manolitto/openvlex2/gluing-stencil/img/gluing_with_base_clamps.jpg

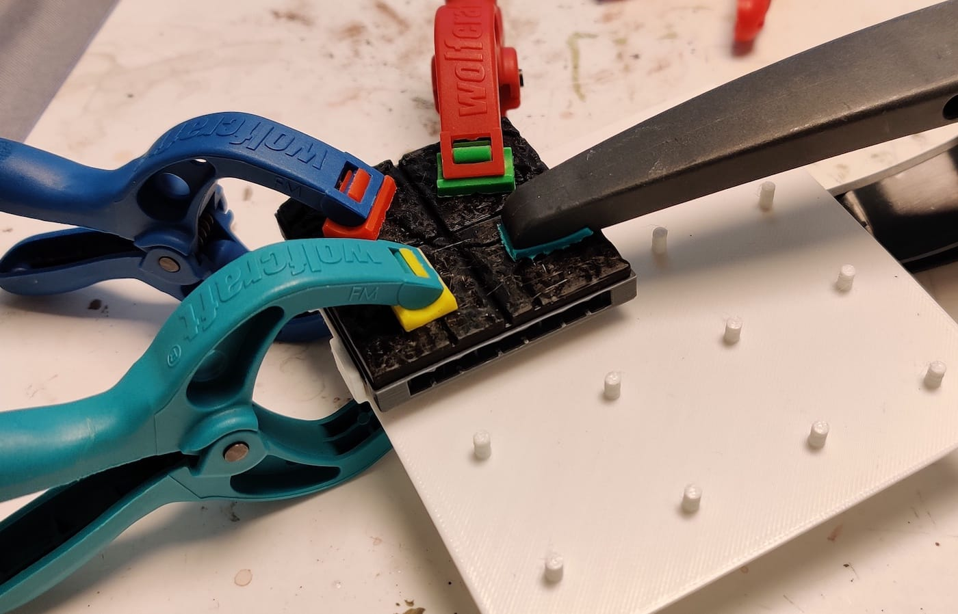
gluing-stencil/img/gluing_with_base_clamps.jpg
