manolitto/openvlex2/gluing-stencil/img/gluing_with_base_clamps_upside_down.jpg

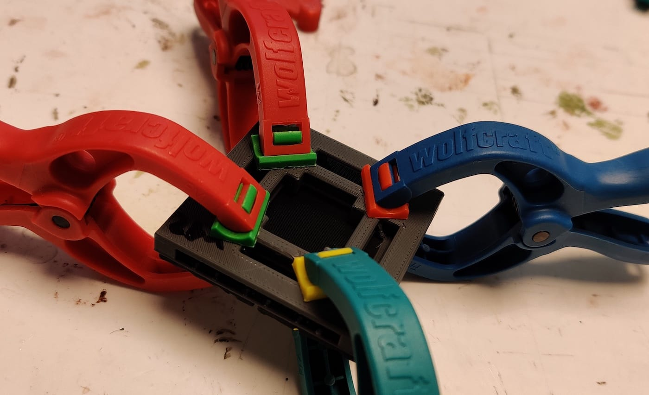
gluing-stencil/img/gluing_with_base_clamps_upside_down.jpg
