manolitto/openvlex2/gluing-stencil/img/gluing_with_base_remove.jpg

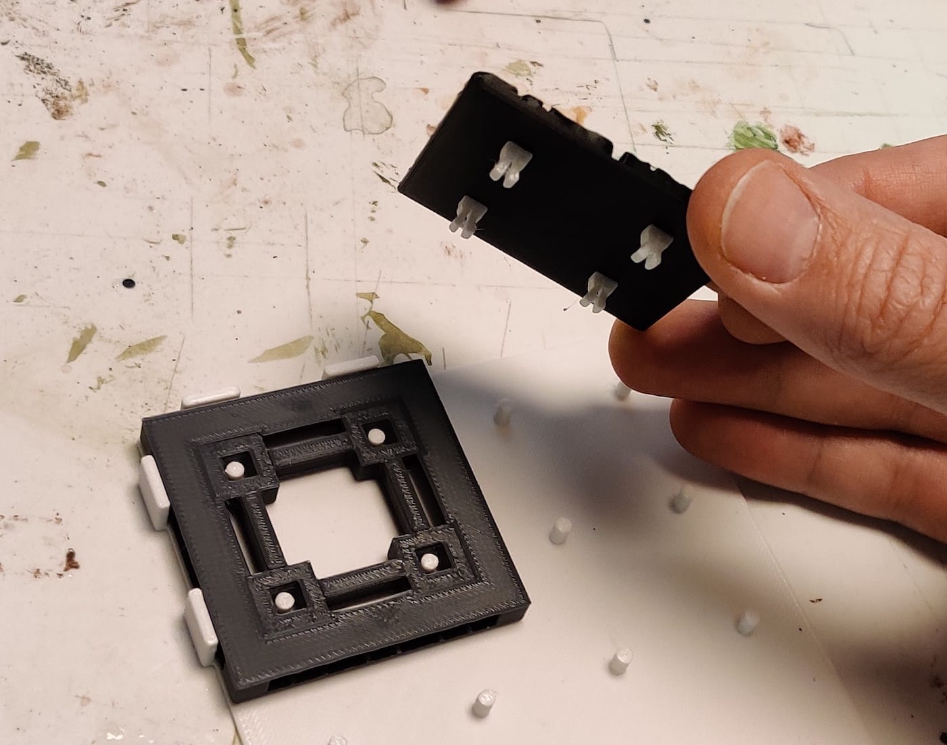
gluing-stencil/img/gluing_with_base_remove.jpg
