manolitto/openvlex2/img/img002.jpg

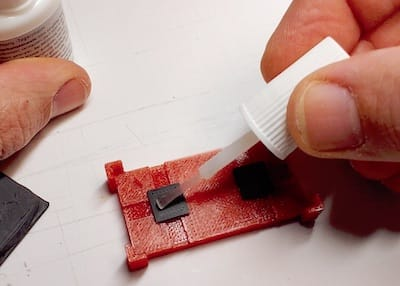
img/img002.jpg
