manolitto/openvlex2/img/img003.jpg

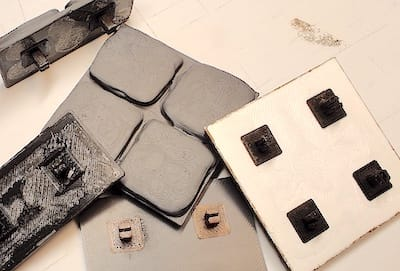
img/img003.jpg
