manolitto/openvlex2/img/img013.jpg

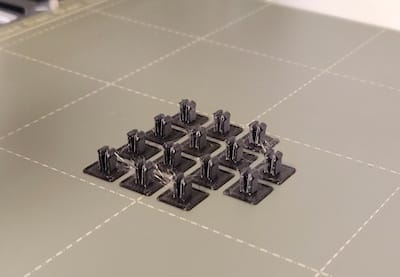
img/img013.jpg
