manolitto/openvlex2/img/stairs/IMG_20210401_234859.jpg

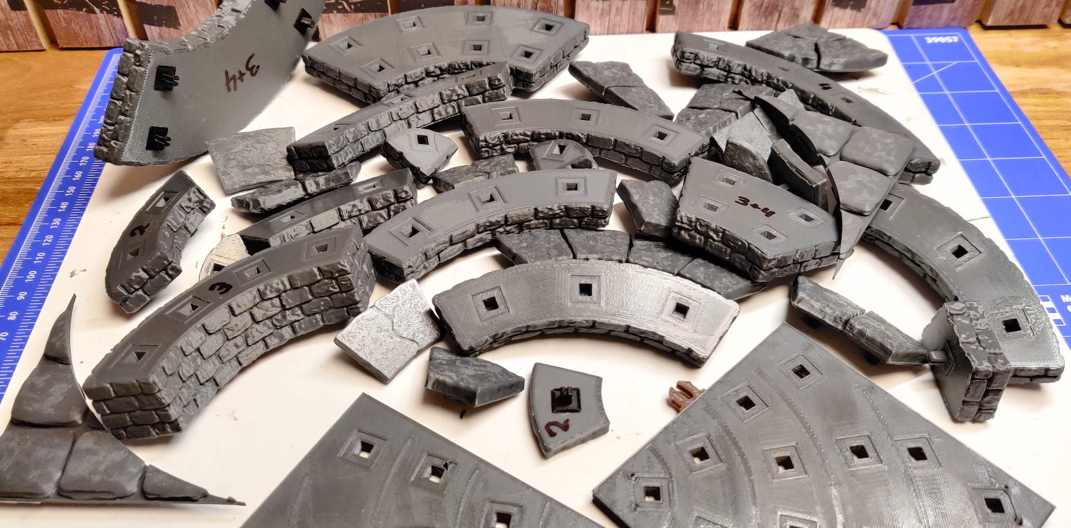
img/stairs/IMG_20210401_234859.jpg
