manolitto/openvlex2/img/stairs/IMG_20210401_235115.jpg

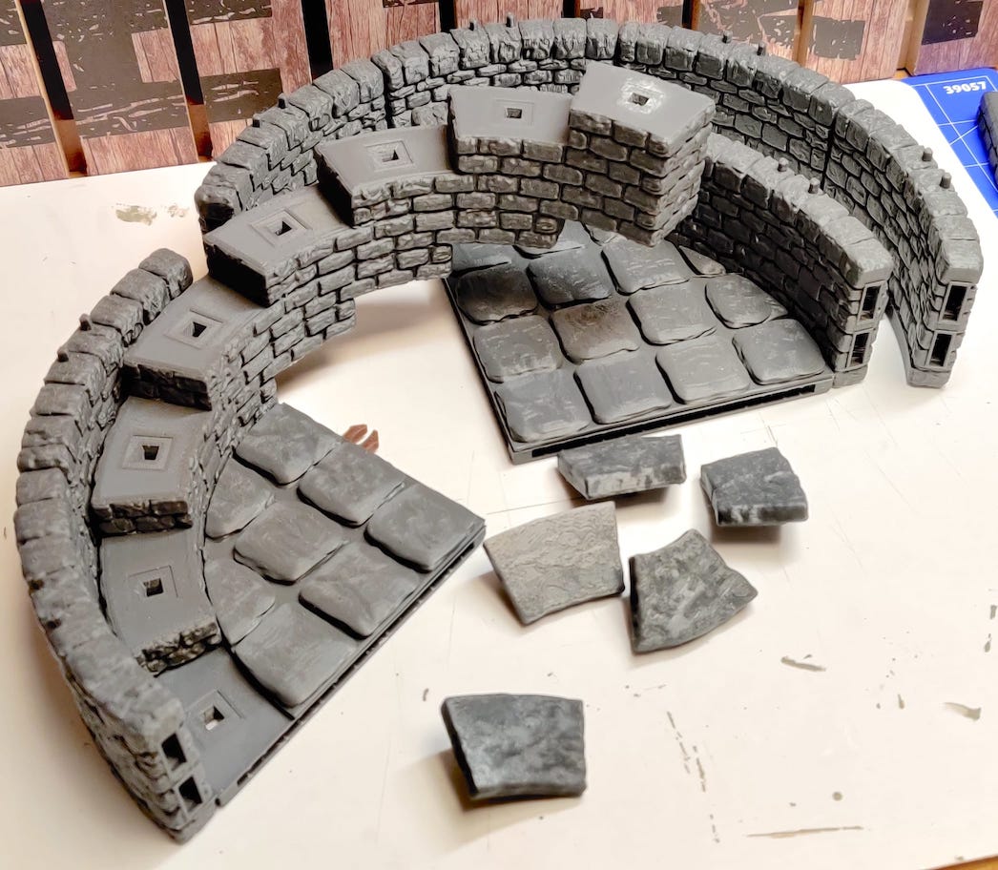
img/stairs/IMG_20210401_235115.jpg
