manolitto/openvlex2/socket_negatives/openvlex.bottom_socket_negative.square.1x1.large.stl

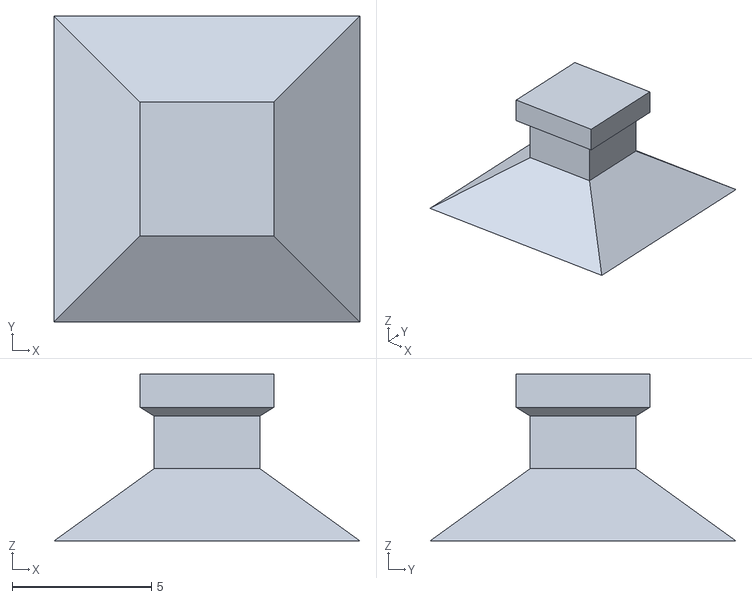
[picture p82: CAD file, 2022-04-11]
socket_negatives/openvlex.bottom_socket_negative.square.1x1.large.stl
11.0 x 11.0 x 6.00
