manolitto/openvlex2/stairs_and_risers/dungeon_stone/curved/dungeon_stone_stairs.curved.inch.riser.1+2x45°x0.25.openvlex.radial.stl

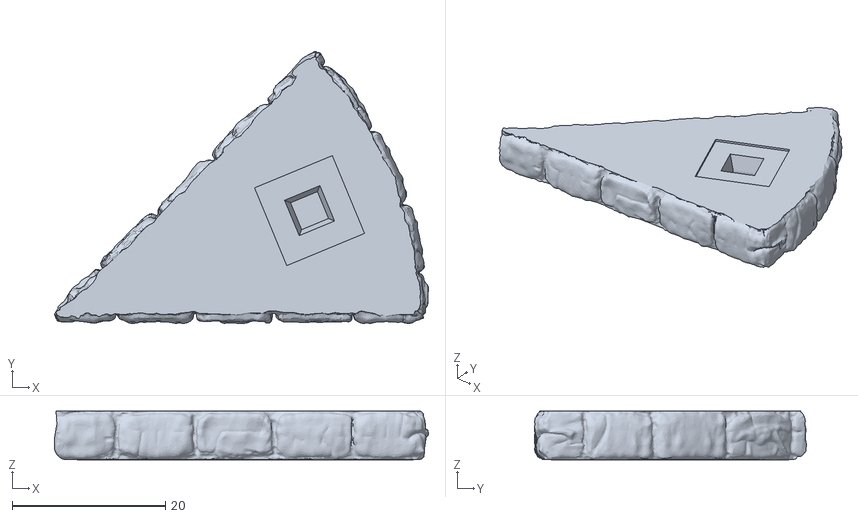
[picture p84: CAD file, 2021-07-12]
stairs_and_risers/dungeon_stone/curved/dungeon_stone_stairs.curved.inch.riser.1+2x45°x0.25.openvlex.radial.stl
48.9 x 35.5 x 6.35
