manolitto/openvlex2/stairs_and_risers/dungeon_stone/square/dungeon_stone_stairs.square.inch.riser_base.1x1x0.5.NS.openvlex.top_and_bottom.stl

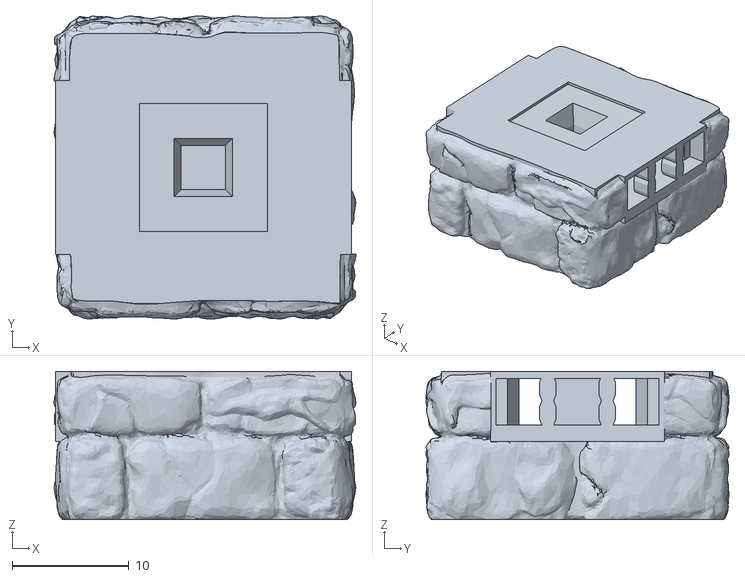
[picture p85: CAD file, 2021-07-12]
stairs_and_risers/dungeon_stone/square/dungeon_stone_stairs.square.inch.riser_base.1x1x0.5.NS.openvlex.top_and_bottom.stl
25.9 x 26.0 x 12.7
