manolitto/openvlex2/stairs_and_risers/plain/backwards_compatible/plain#riser+square,interlayer_half.2x2.openvlex,backwards_compatible.stl

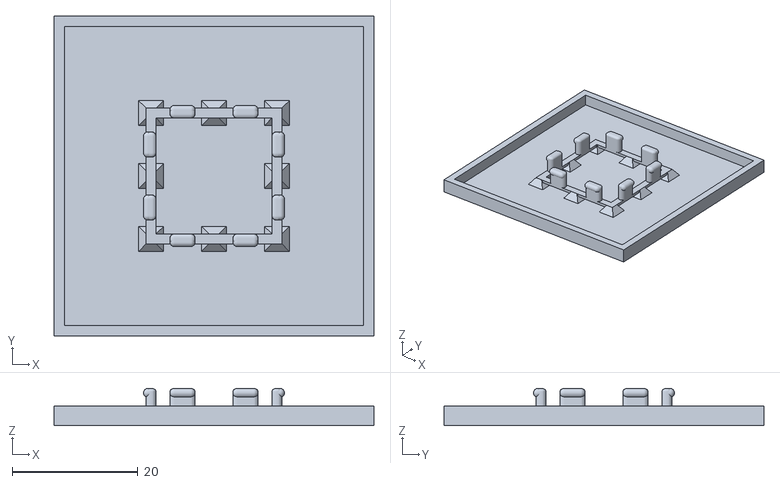
[picture p86: CAD file, 2022-01-03]
stairs_and_risers/plain/backwards_compatible/plain#riser+square,interlayer_half.2x2.openvlex,backwards_compatible.stl
50.8 x 50.8 x 5.90
