manolitto/openvlex2/stairs_and_risers/roof/roof+attic_support_block.4x.stl

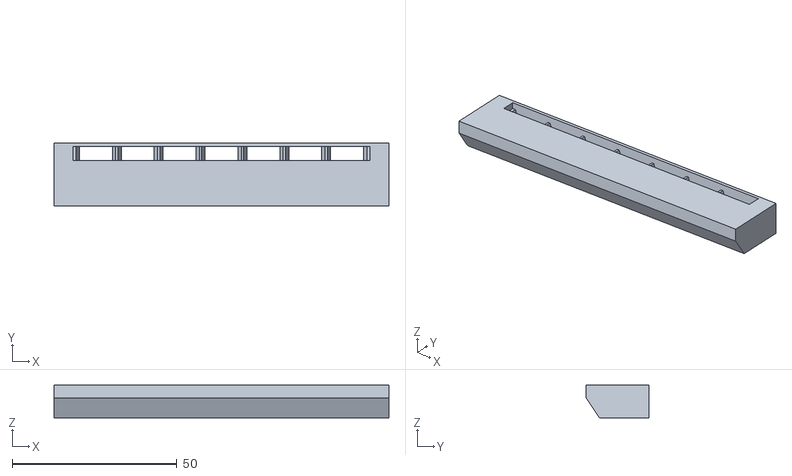
[picture p88: CAD file, 2022-01-11]
stairs_and_risers/roof/roof+attic_support_block.4x.stl
101.6 x 19.0 x 10.0
