manolitto/openvlex2/stairs_and_risers/towne/square/towne_stairs.square.inch.riser.1x1x1.0.openvlex.stl

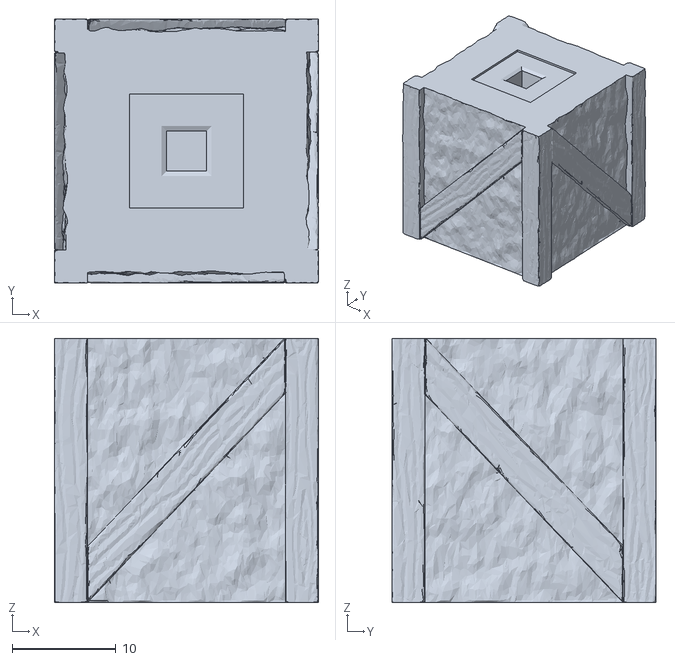
[picture p89: CAD file, 2021-04-06]
stairs_and_risers/towne/square/towne_stairs.square.inch.riser.1x1x1.0.openvlex.stl
25.4 x 25.4 x 25.4
