manolitto/openvlex2/storage/openvlex.storage_base_clip.floor.2_inch.stl

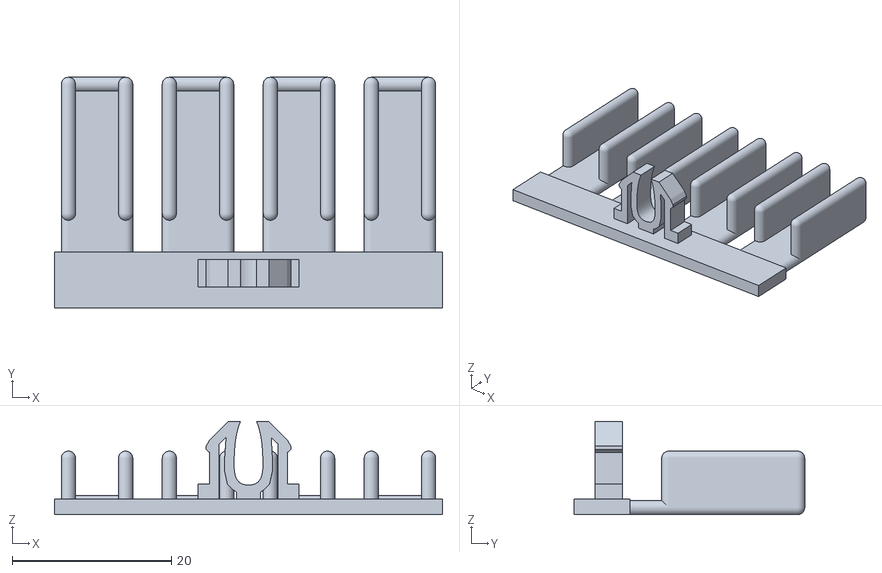
[picture p90: CAD file, 2021-04-06]
storage/openvlex.storage_base_clip.floor.2_inch.stl
48.8 x 29.0 x 11.7
