manolitto/openvlex2/bases/plain/magnetic,openlock,openvlex+dual_parts/plain#base+square.7x3.magnetic,openlock,openvlex+lower_part.stl

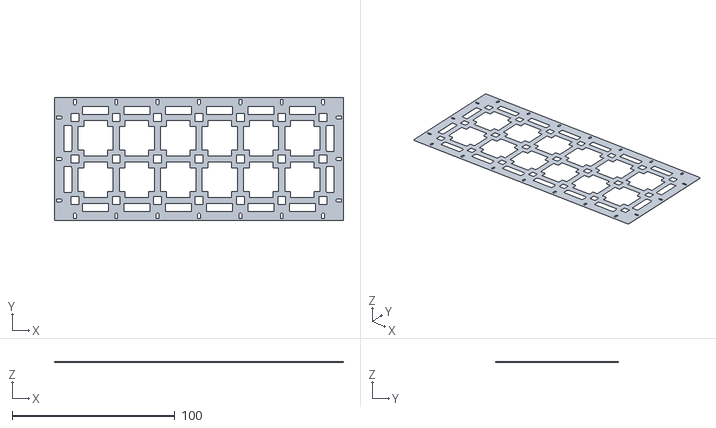
[picture p92: CAD file, 2022-01-04]
bases/plain/magnetic,openlock,openvlex+dual_parts/plain#base+square.7x3.magnetic,openlock,openvlex+lower_part.stl
177.4 x 75.8 x 0.6
