manolitto/openvlex2/bases/plain/magnetic,openlock,openvlex+radial/plain#base+square.4x4.magnetic.openlock,openvlex+radial,upper_part.stl

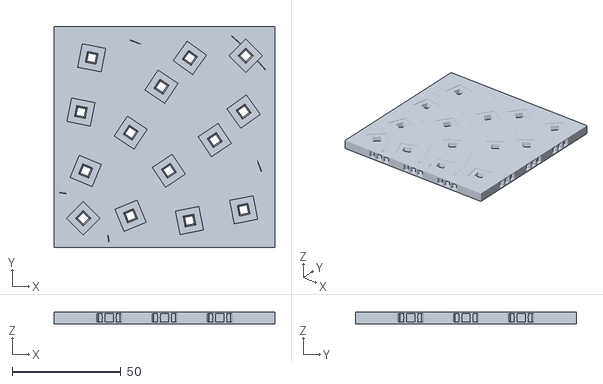
[picture p93: CAD file, 2021-11-02]
bases/plain/magnetic,openlock,openvlex+radial/plain#base+square.4x4.magnetic.openlock,openvlex+radial,upper_part.stl
101.6 x 101.6 x 5.40
