manolitto/openvlex2/bases/plain/openlock,openflex+radial/plain#base+square.2x2.openlock,openvlex+radial.stl

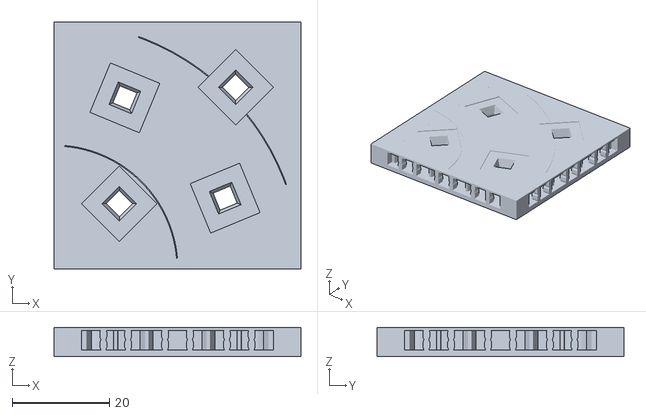
[picture p94: CAD file, 2021-11-02]
bases/plain/openlock,openflex+radial/plain#base+square.2x2.openlock,openvlex+radial.stl
50.8 x 50.8 x 6.01
