manolitto/openvlex2/bases/plain/POC/base.plain.square.inch.2x2.magnetic.openlock.openvlex_upper.stl

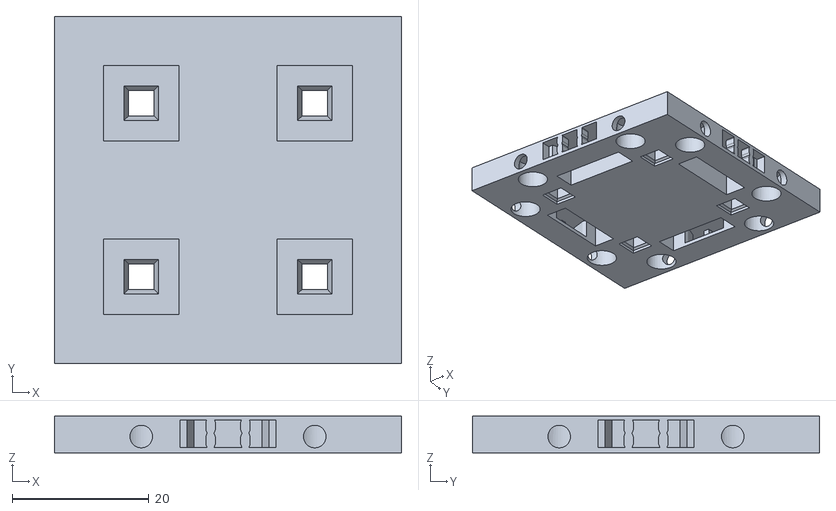
[picture p96: CAD file, 2021-11-02]
bases/plain/POC/base.plain.square.inch.2x2.magnetic.openlock.openvlex_upper.stl
50.8 x 50.8 x 5.40
