manolitto/openvlex2/bases/separate_wall/rough_stone#base.A.openlock,openvlex.stl

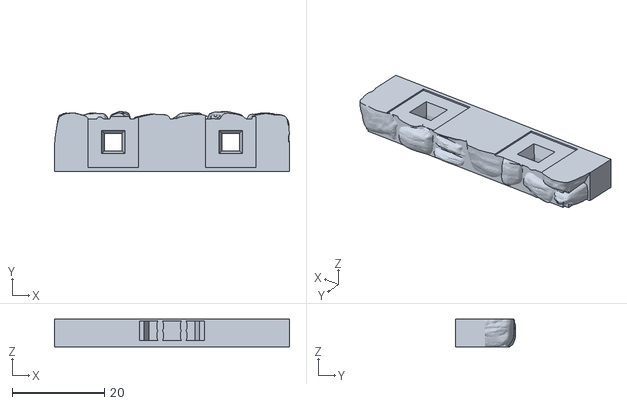
[picture p97: CAD file, 2022-01-12]
bases/separate_wall/rough_stone#base.A.openlock,openvlex.stl
50.8 x 13.0 x 6.00
