manolitto/openvlex2/bases/sewer/sewer#base+square.1x1.openlock,openvlex+corner.stl

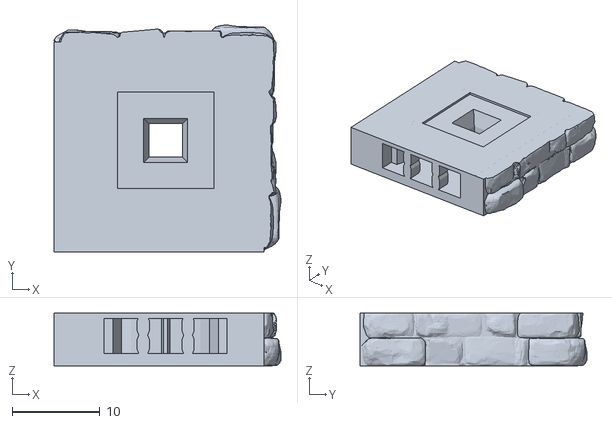
[picture p98: CAD file, 2021-11-30]
bases/sewer/sewer#base+square.1x1.openlock,openvlex+corner.stl
25.8 x 25.8 x 6.01
