manolitto/openvlex2/gluing-stencil/openvlex_gluing_stencil.4x3.stl

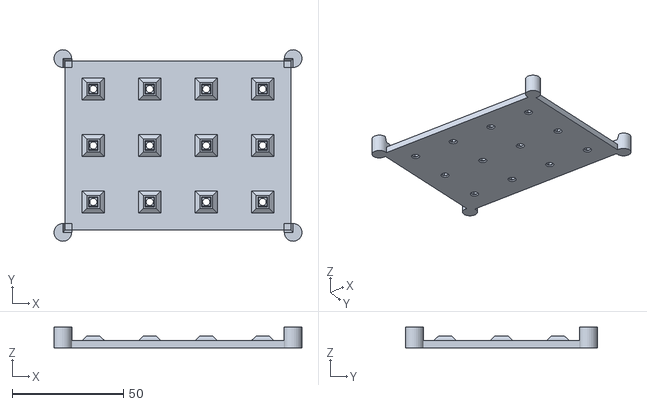
[picture p99: CAD file, 2022-04-11]
gluing-stencil/openvlex_gluing_stencil.4x3.stl
111.6 x 86.2 x 9.40
