manolitto/openvlex2/jacks/openvlex.double_jack (v2.5.0).stl

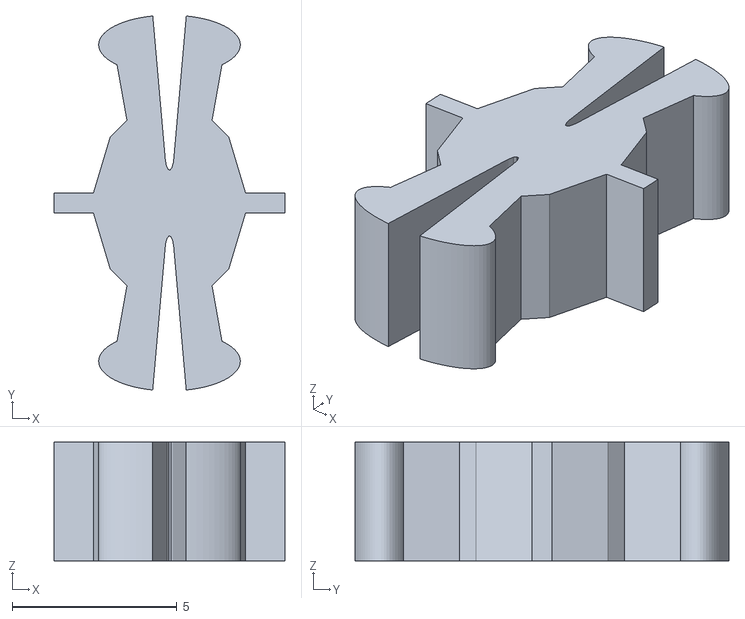
[picture p100: CAD file, 2022-04-11]
jacks/openvlex.double_jack (v2.5.0).stl
7.00 x 11.3 x 3.60
