manolitto/openvlex2/openflex1_to_openvlex2_adapter/openflex1_to_openvlex2_adapter_plate.small.1x1.stl

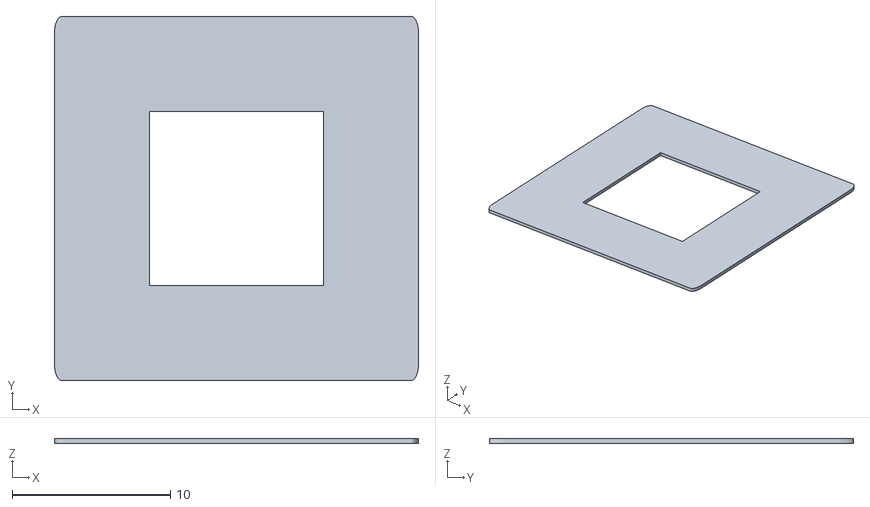
[picture p101: CAD file, 2021-03-14]
openflex1_to_openvlex2_adapter/openflex1_to_openvlex2_adapter_plate.small.1x1.stl
23.0 x 23.0 x 0.296
