manolitto/openvlex2/socket_negatives/openvlex.bottom_socket_negative.square.4x2.square.stl

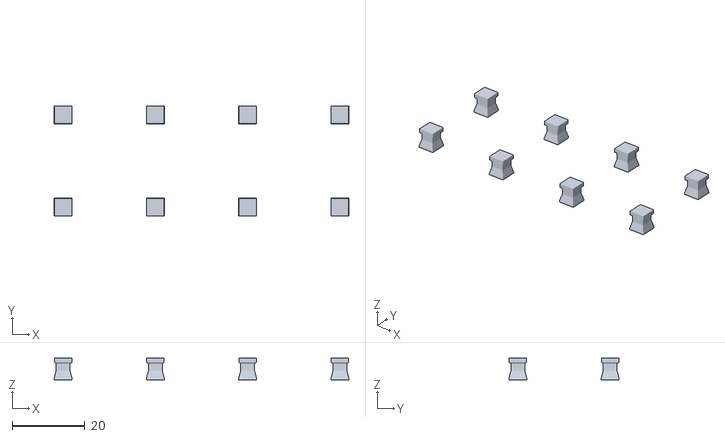
[picture p102: CAD file, 2021-04-16]
socket_negatives/openvlex.bottom_socket_negative.square.4x2.square.stl
81.2 x 30.4 x 6.00
