manolitto/openvlex2/stairs_and_risers/dungeon_stone/curved/dungeon_stone_stairs.curved.inch.riser.4x45°x0.5.openvlex.radial.stl

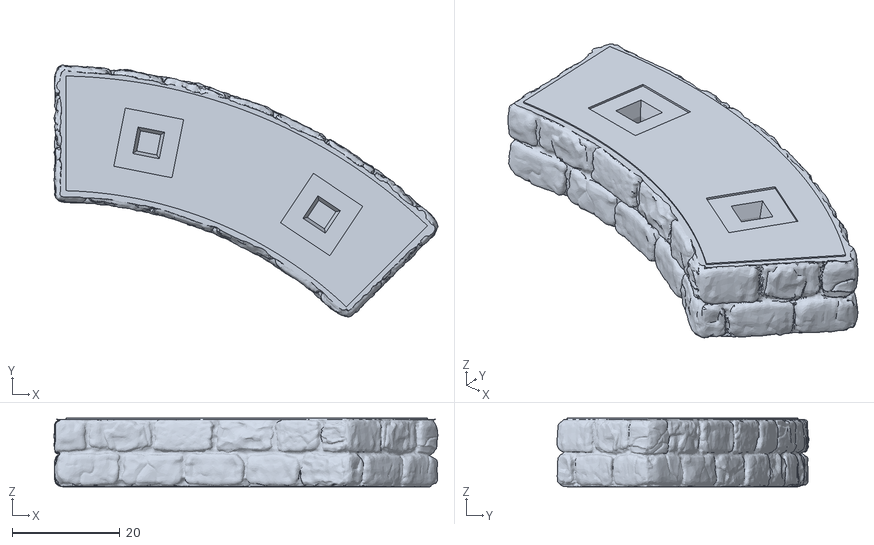
[picture p104: CAD file, 2021-03-31]
stairs_and_risers/dungeon_stone/curved/dungeon_stone_stairs.curved.inch.riser.4x45°x0.5.openvlex.radial.stl
71.1 x 46.7 x 12.7
