manolitto/openvlex2/stairs_and_risers/plain/backwards_compatible/plain#riser+square,platform.2x2.openvlex,backwards_compatible.stl

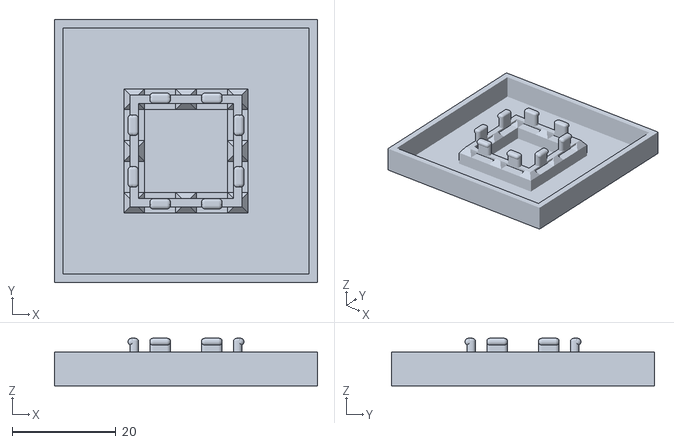
[picture p106: CAD file, 2022-01-03]
stairs_and_risers/plain/backwards_compatible/plain#riser+square,platform.2x2.openvlex,backwards_compatible.stl
50.8 x 50.8 x 9.20
