manolitto/openvlex2/stairs_and_risers/plain/plain#riser+square,platform.1x1.openvlex.stl

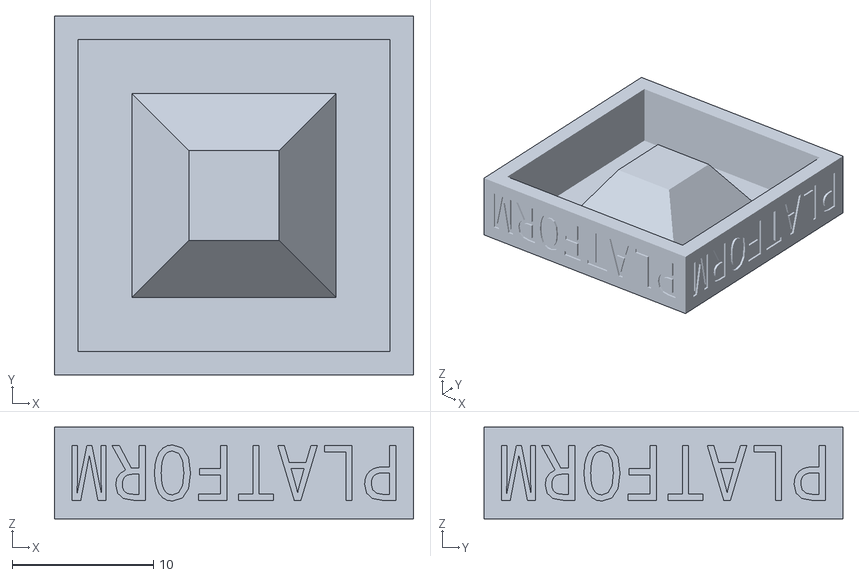
[picture p107: CAD file, 2022-04-11]
stairs_and_risers/plain/plain#riser+square,platform.1x1.openvlex.stl
25.4 x 25.4 x 6.50
