manolitto/openvlex2/stairs_and_risers/towne/square/towne_stairs.square.inch.riser.2x2x1.0.openvlex.stl

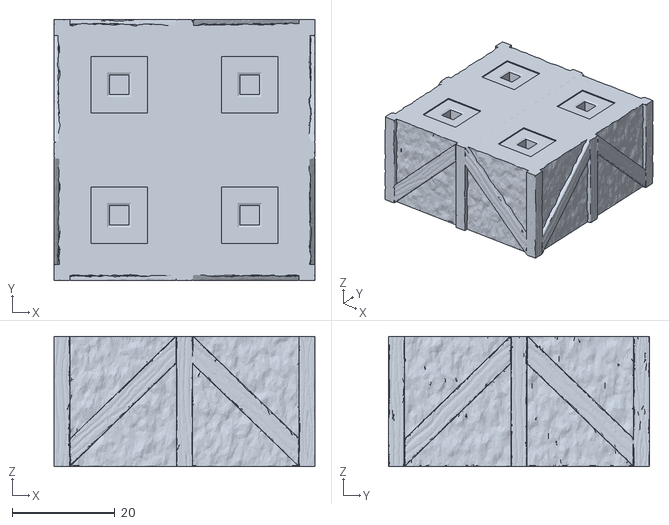
[picture p108: CAD file, 2021-04-06]
stairs_and_risers/towne/square/towne_stairs.square.inch.riser.2x2x1.0.openvlex.stl
50.8 x 50.8 x 25.4
