manolitto/openvlex2/bases/dungeon_stone/dungeon_stone#base+square.2x1.openlock,openvlex+corner-left.stl

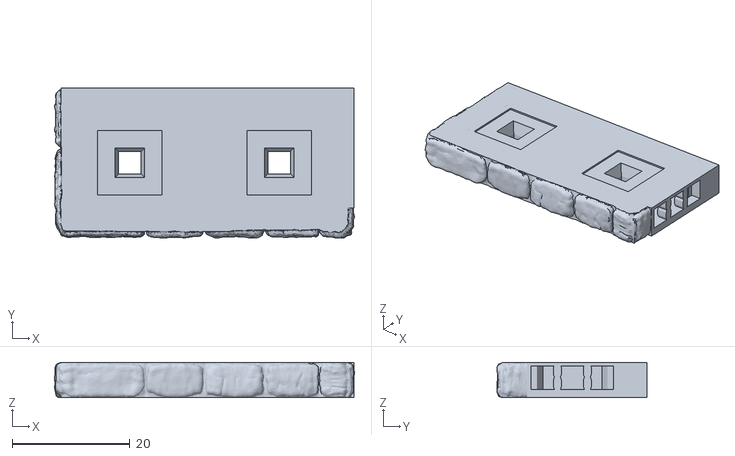
[picture p109: CAD file, 2021-04-17]
bases/dungeon_stone/dungeon_stone#base+square.2x1.openlock,openvlex+corner-left.stl
51.0 x 25.5 x 6.01
