manolitto/openvlex2/bases/plain/magnetic,openlock,openvlex+dual_parts/plain#base+square.8x5.magnetic,openlock,openvlex+border_only,lower_part.stl

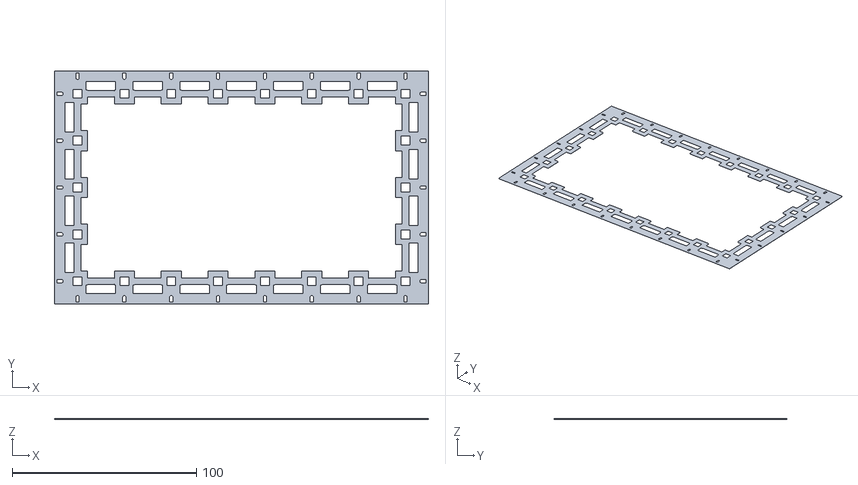
[picture p110: CAD file, 2022-01-04]
bases/plain/magnetic,openlock,openvlex+dual_parts/plain#base+square.8x5.magnetic,openlock,openvlex+border_only,lower_part.stl
202.8 x 126.6 x 0.6
