manolitto/openvlex2/bases/plain/magnetic,openlock,openvlex+radial/plain#base+square.2x2.magnetic.openlock,openvlex+radial,upper_part.stl

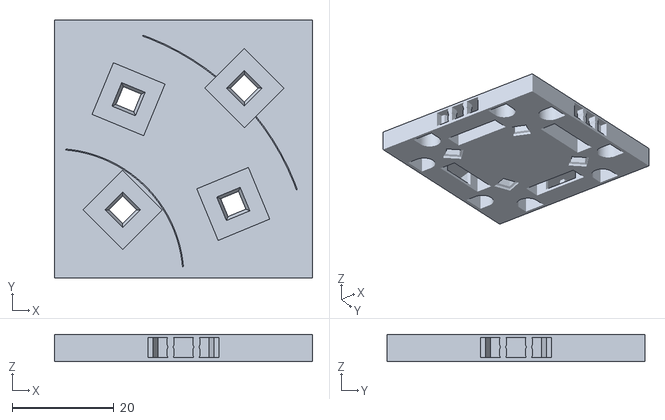
[picture p111: CAD file, 2021-11-02]
bases/plain/magnetic,openlock,openvlex+radial/plain#base+square.2x2.magnetic.openlock,openvlex+radial,upper_part.stl
50.8 x 50.8 x 5.40
