manolitto/openvlex2/bases/plain/openlock,openflex+radial/plain#base+square.3x3.openlock,openvlex+radial.stl

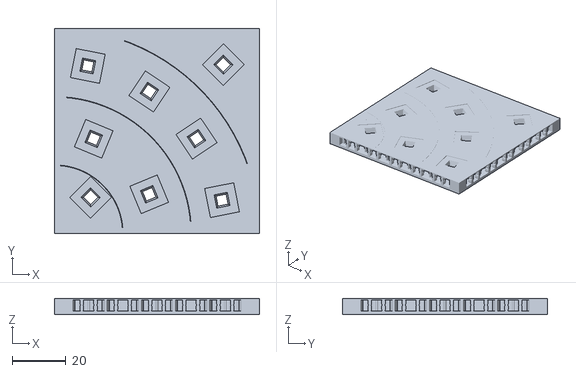
[picture p113: CAD file, 2021-11-02]
bases/plain/openlock,openflex+radial/plain#base+square.3x3.openlock,openvlex+radial.stl
76.2 x 76.2 x 6.01
