manolitto/openvlex2/bases/plain/openlock,openvlex/plain#base+square.8x3.openlock,openvlex+border_only.stl

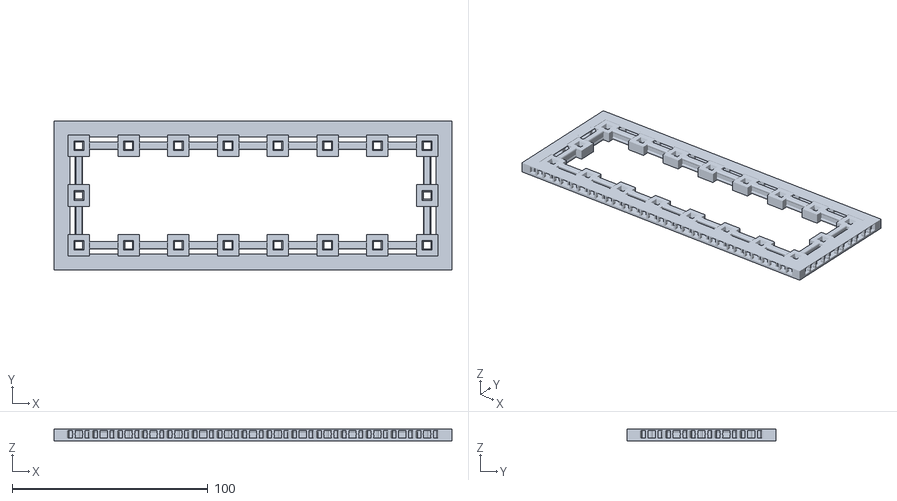
[picture p114: CAD file, 2022-01-04]
bases/plain/openlock,openvlex/plain#base+square.8x3.openlock,openvlex+border_only.stl
203.2 x 76.2 x 6.01
