manolitto/openvlex2/bases/sewer/sewer#base+square.2x1.openlock,openvlex+edge.stl

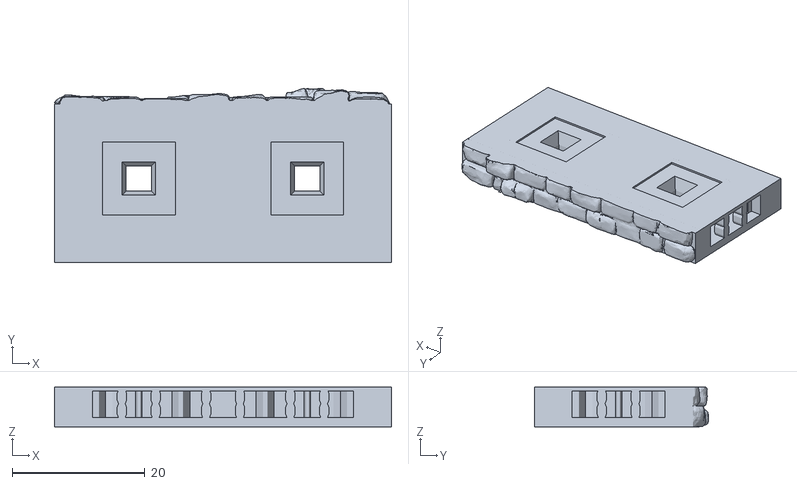
[picture p115: CAD file, 2021-11-30]
bases/sewer/sewer#base+square.2x1.openlock,openvlex+edge.stl
50.8 x 26.3 x 6.01
