manolitto/openvlex2/gluing-stencil/openvlex_gluing_stencil.4x2.stl

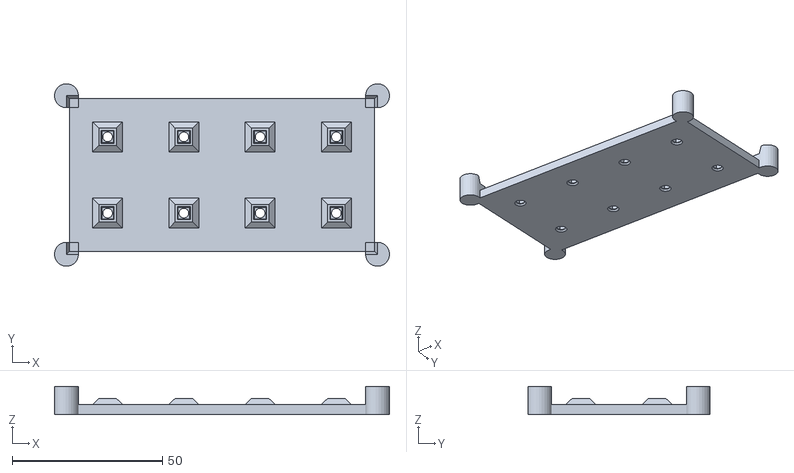
[picture p116: CAD file, 2022-04-11]
gluing-stencil/openvlex_gluing_stencil.4x2.stl
111.6 x 60.8 x 9.40
