manolitto/openvlex2/openflex1_to_openvlex2_adapter/openflex1_to_openvlex2_adapter_plate.small.2x1.stl

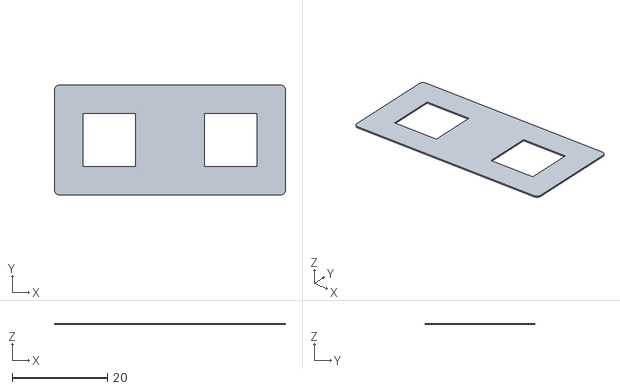
[picture p117: CAD file, 2021-03-14]
openflex1_to_openvlex2_adapter/openflex1_to_openvlex2_adapter_plate.small.2x1.stl
48.4 x 23.0 x 0.296
