manolitto/openvlex2/socket_negatives/openvlex.top_socket_negative.square.4x2.square.stl

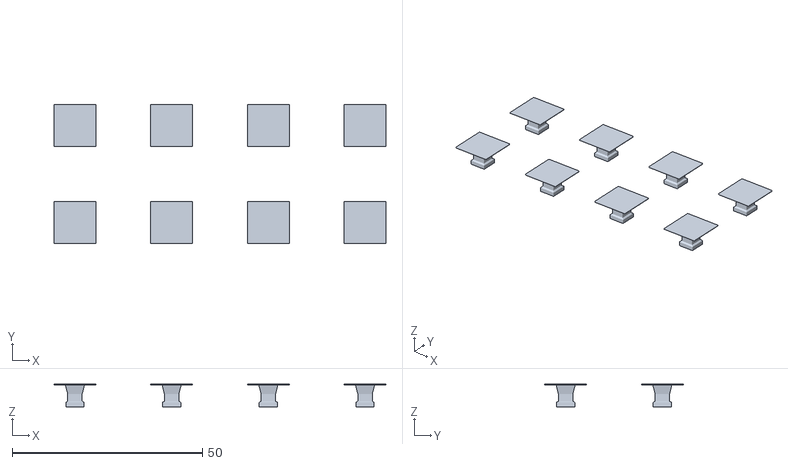
[picture p118: CAD file, 2021-04-16]
socket_negatives/openvlex.top_socket_negative.square.4x2.square.stl
87.2 x 36.4 x 6.00
