manolitto/openvlex2/stairs_and_risers/cut_stone/square/cut_stone_stairs.square.inch.riser.2x2x0.5.openvlex.stl

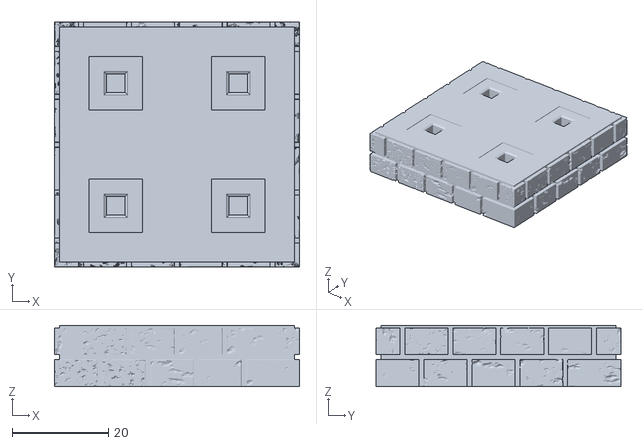
[picture p119: CAD file, 2021-04-06]
stairs_and_risers/cut_stone/square/cut_stone_stairs.square.inch.riser.2x2x0.5.openvlex.stl
50.8 x 50.8 x 12.7
