manolitto/openvlex2/stairs_and_risers/dungeon_stone/curved/dungeon_stone_stairs.curved.inch.riser.1+2x45°x0.5.openvlex.radial.stl

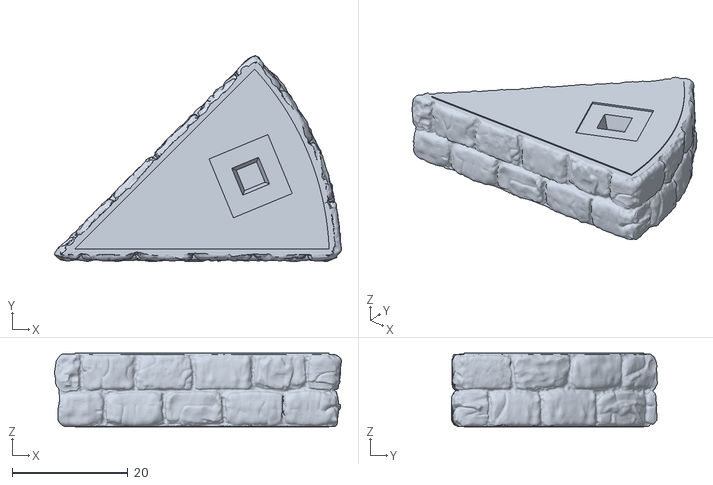
[picture p120: CAD file, 2021-03-27]
stairs_and_risers/dungeon_stone/curved/dungeon_stone_stairs.curved.inch.riser.1+2x45°x0.5.openvlex.radial.stl
49.6 x 35.6 x 12.7
