manolitto/openvlex2/stairs_and_risers/plain/plain#riser+square,low.2x2.openvlex,L-shape.stl

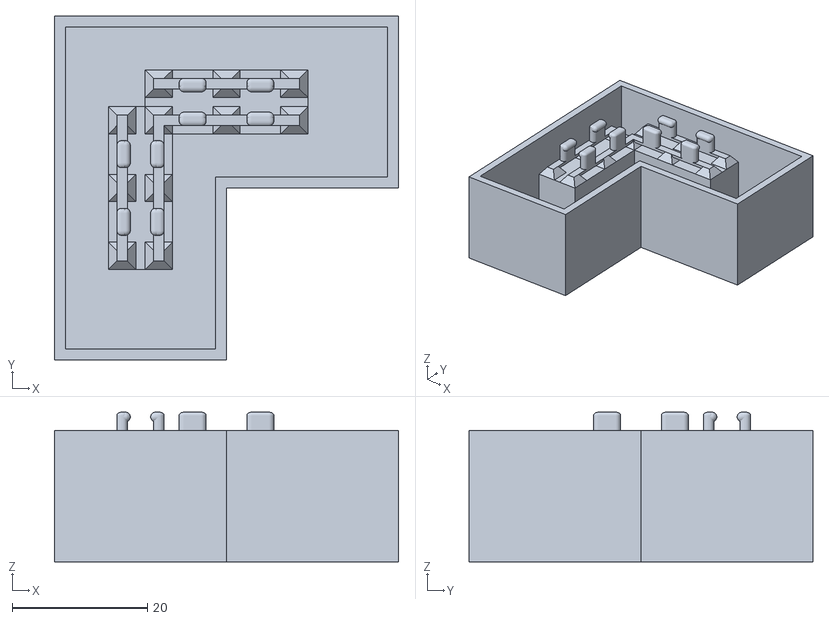
[picture p122: CAD file, 2022-04-11]
stairs_and_risers/plain/plain#riser+square,low.2x2.openvlex,L-shape.stl
50.8 x 50.8 x 22.1
