manolitto/openvlex2/stairs_and_risers/towne/square/towne_stairs.square.inch.riser.2x1x1.0.openvlex.stl

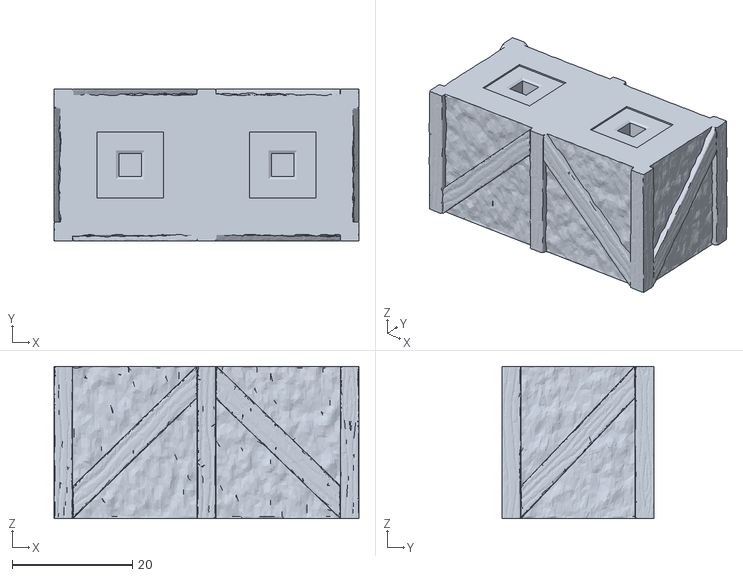
[picture p123: CAD file, 2021-04-06]
stairs_and_risers/towne/square/towne_stairs.square.inch.riser.2x1x1.0.openvlex.stl
50.8 x 25.4 x 25.4
