manolitto/openvlex2/bases/dungeon_stone/dungeon_stone#base+square.1x1.openlock,openvlex+corner.stl

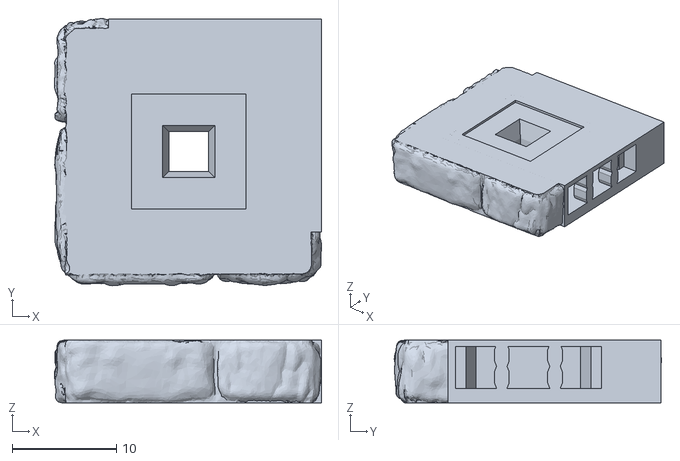
[picture p124: CAD file, 2021-04-17]
bases/dungeon_stone/dungeon_stone#base+square.1x1.openlock,openvlex+corner.stl
25.6 x 25.6 x 6.01
