manolitto/openvlex2/bases/plain/magnetic,openlock,openvlex+dual_parts/plain#base+square.4x4.magnetic,openlock,openvlex+border_only,lower_part.stl

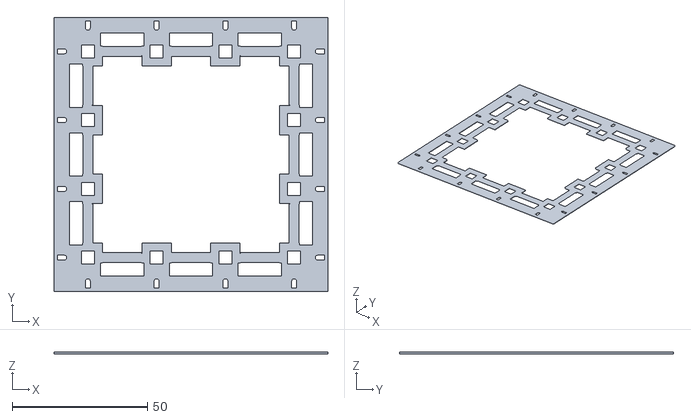
[picture p125: CAD file, 2022-01-04]
bases/plain/magnetic,openlock,openvlex+dual_parts/plain#base+square.4x4.magnetic,openlock,openvlex+border_only,lower_part.stl
101.2 x 101.2 x 0.6
