manolitto/openvlex2/bases/plain/magnetic,openlock,openvlex+radial/plain#base+square.3x3.magnetic.openlock,openvlex+radial,upper_part.stl

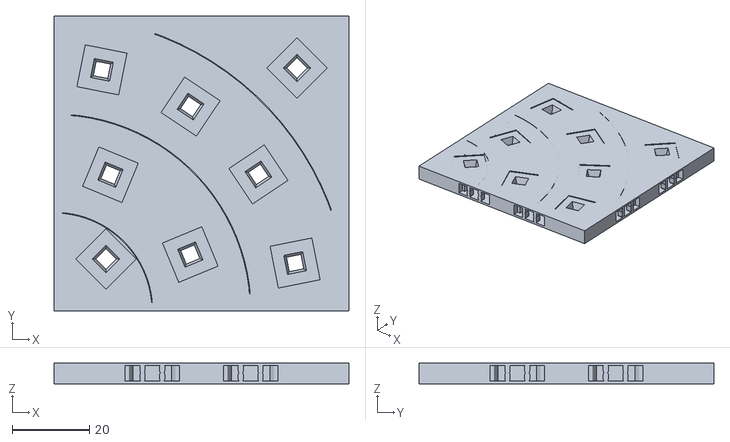
[picture p126: CAD file, 2021-11-02]
bases/plain/magnetic,openlock,openvlex+radial/plain#base+square.3x3.magnetic.openlock,openvlex+radial,upper_part.stl
76.2 x 76.2 x 5.40
