manolitto/openvlex2/bases/plain/openlock,openvlex/plain#base+square.7x7.openlock,openvlex+border_only.stl

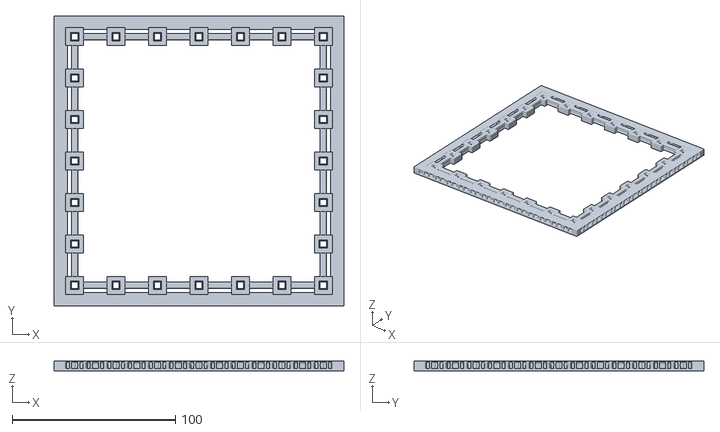
[picture p127: CAD file, 2022-01-04]
bases/plain/openlock,openvlex/plain#base+square.7x7.openlock,openvlex+border_only.stl
177.8 x 177.8 x 6.01
