manolitto/openvlex2/gluing-stencil/openvlex_gluing_stencil.4x1.stl

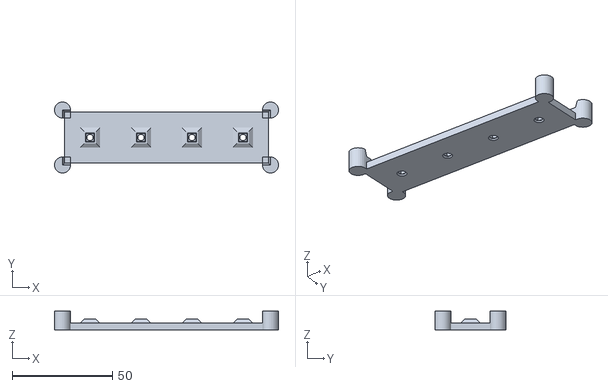
[picture p128: CAD file, 2022-04-11]
gluing-stencil/openvlex_gluing_stencil.4x1.stl
111.6 x 35.4 x 9.40
