manolitto/openvlex2/openflex1_to_openvlex2_adapter/openflex1_to_openvlex2_adapter_socket_with_support.stl

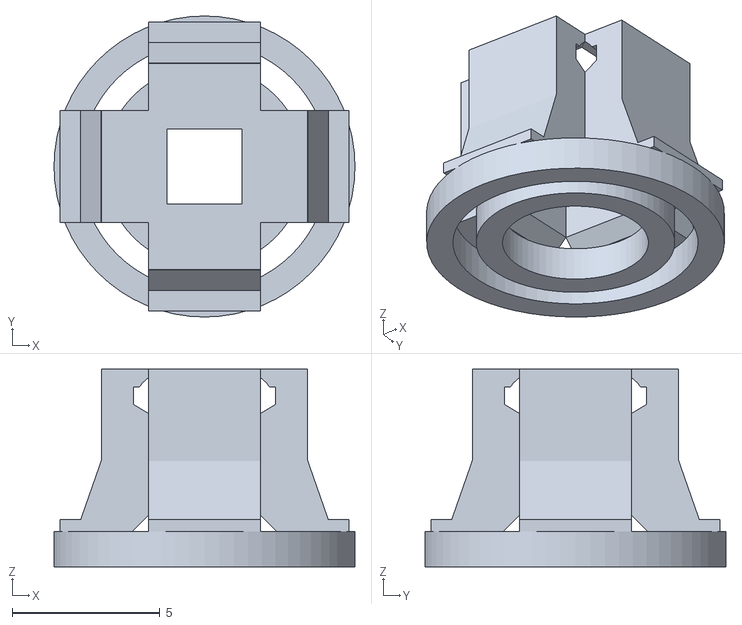
[picture p129: CAD file, 2021-03-14]
openflex1_to_openvlex2_adapter/openflex1_to_openvlex2_adapter_socket_with_support.stl
10.2 x 10.2 x 6.70
