manolitto/openvlex2/socket_negatives/openvlex.bottom_socket_negative.square.2x1.square.stl

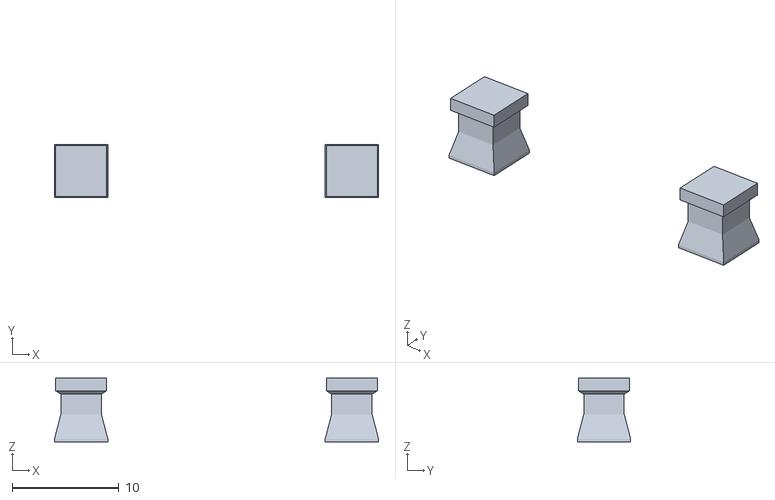
[picture p130: CAD file, 2021-04-16]
socket_negatives/openvlex.bottom_socket_negative.square.2x1.square.stl
30.4 x 5.00 x 6.00
