manolitto/openvlex2/stairs_and_risers/dungeon_stone/curved/dungeon_stone_stairs.curved.inch.riser.3x90°x0.5.openvlex.radial.stl

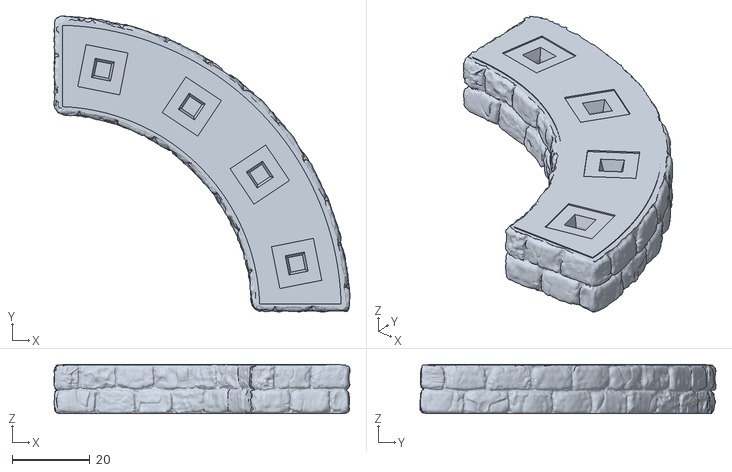
[picture p131: CAD file, 2021-03-27]
stairs_and_risers/dungeon_stone/curved/dungeon_stone_stairs.curved.inch.riser.3x90°x0.5.openvlex.radial.stl
76.2 x 76.2 x 12.7
