manolitto/openvlex2/stairs_and_risers/dungeon_stone/square/dungeon_stone_stairs.square.inch.riser_base.2x2x1.0.NE.openvlex.stl

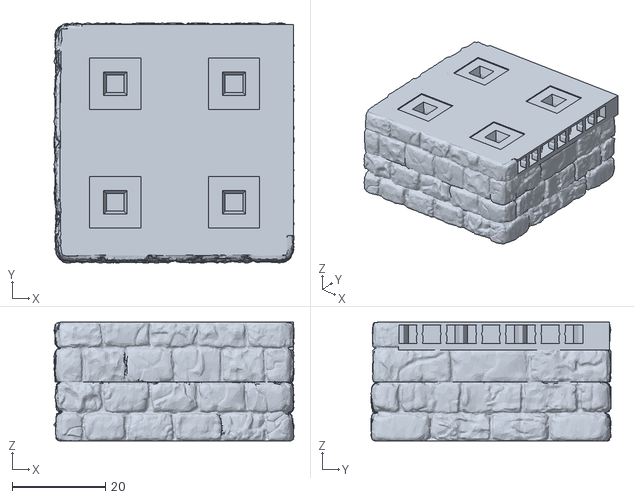
[picture p132: CAD file, 2021-07-12]
stairs_and_risers/dungeon_stone/square/dungeon_stone_stairs.square.inch.riser_base.2x2x1.0.NE.openvlex.stl
51.4 x 51.4 x 25.4
