manolitto/openvlex2/stairs_and_risers/plain/plain#riser+square,platform.2x2.openvlex.stl

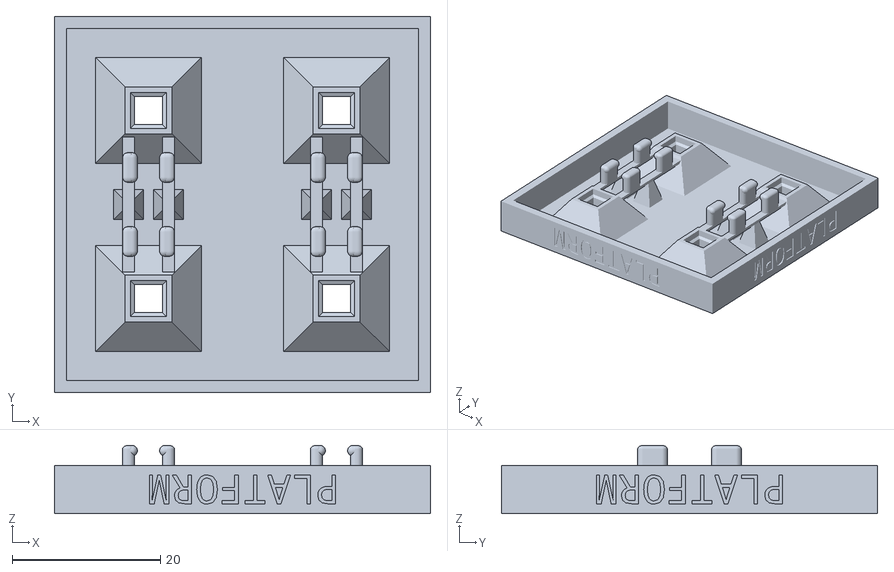
[picture p133: CAD file, 2022-04-11]
stairs_and_risers/plain/plain#riser+square,platform.2x2.openvlex.stl
50.8 x 50.8 x 9.20
