manolitto/openvlex2/bases/plain/magnetic,openlock,openvlex+dual_parts/plain#base+square.6x3.magnetic,openlock,openvlex+upper_part.stl

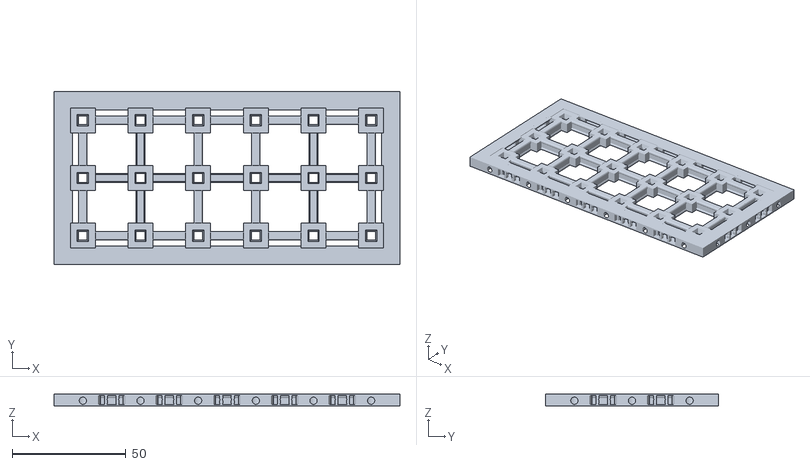
[picture p135: CAD file, 2022-01-04]
bases/plain/magnetic,openlock,openvlex+dual_parts/plain#base+square.6x3.magnetic,openlock,openvlex+upper_part.stl
152.4 x 76.2 x 5.40
