manolitto/openvlex2/bases/plain/magnetic,openlock,openvlex+radial/plain#base+square.3x3.magnetic.openlock,openvlex+radial,lower_part.stl

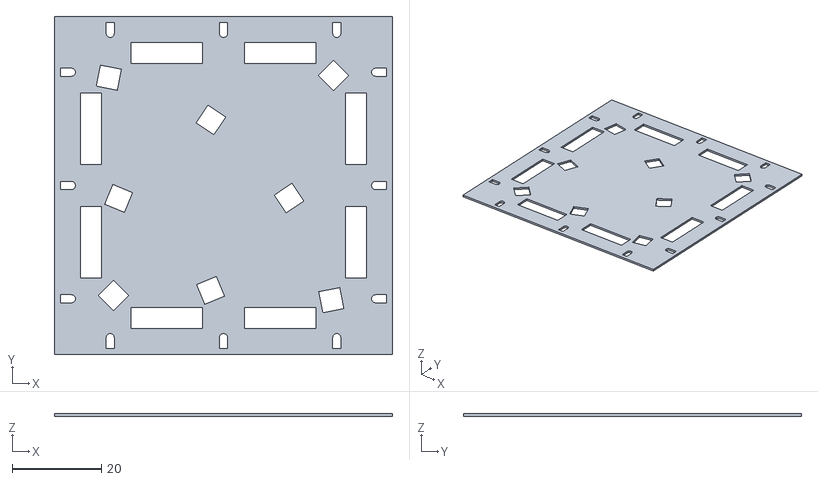
[picture p136: CAD file, 2021-11-02]
bases/plain/magnetic,openlock,openvlex+radial/plain#base+square.3x3.magnetic.openlock,openvlex+radial,lower_part.stl
75.8 x 75.8 x 0.6
