manolitto/openvlex2/bases/plain/magnetic,openlock,openvlex+single_part/plain#base+square.2x1.magnetic,openlock,MMOOOM,openvlex+single_part.stl

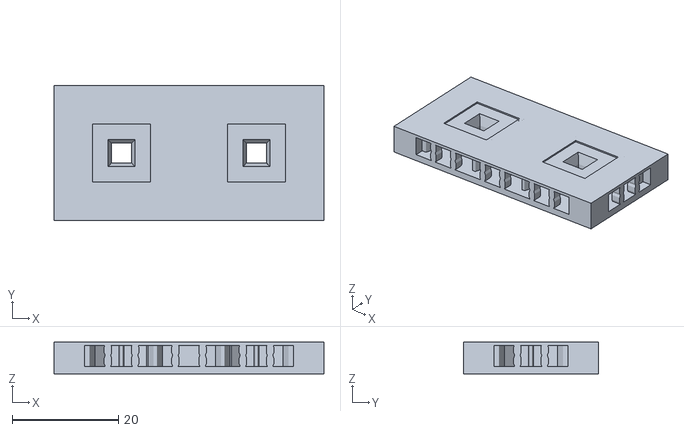
[picture p137: CAD file, 2022-04-11]
bases/plain/magnetic,openlock,openvlex+single_part/plain#base+square.2x1.magnetic,openlock,MMOOOM,openvlex+single_part.stl
50.8 x 25.4 x 6.01
