manolitto/openvlex2/bases/plain/openlock,openvlex/plain#base+square.5x5.openlock,openvlex+border_only.stl

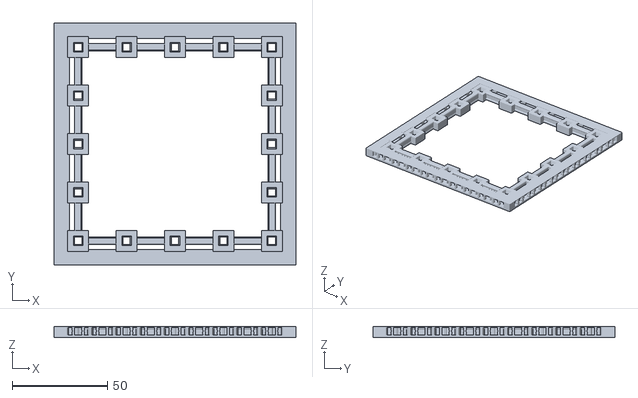
[picture p138: CAD file, 2022-01-04]
bases/plain/openlock,openvlex/plain#base+square.5x5.openlock,openvlex+border_only.stl
127.0 x 127.0 x 6.01
