manolitto/openvlex2/gluing-stencil/openvlex_gluing_stencil.4x4,material_saving.stl

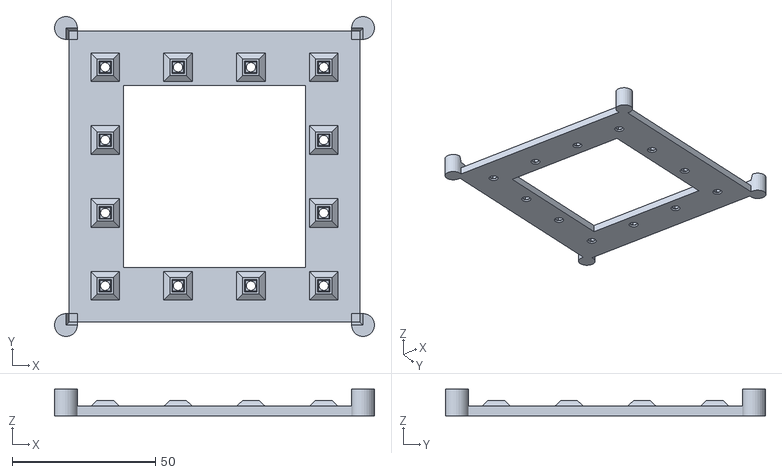
[picture p139: CAD file, 2022-04-11]
gluing-stencil/openvlex_gluing_stencil.4x4,material_saving.stl
111.6 x 111.6 x 9.40
