manolitto/openvlex2/openflex1_to_openvlex2_adapter/openflex1_to_openvlex2_adapter_plate.large.2x2.stl

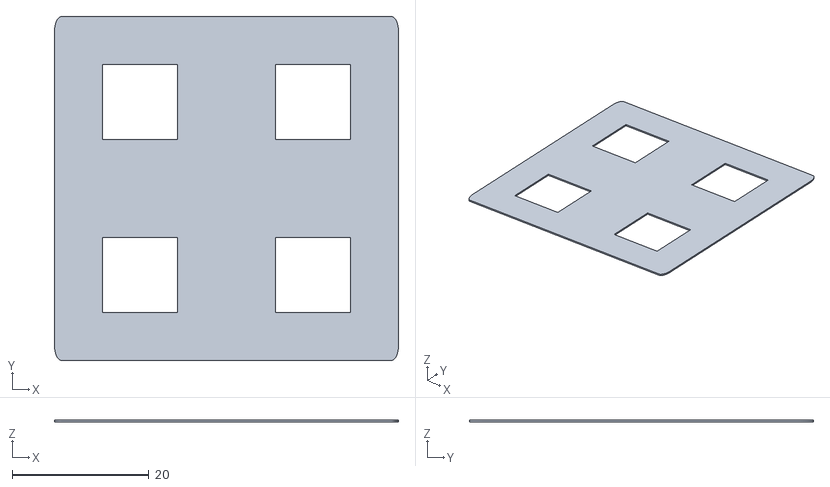
[picture p140: CAD file, 2021-03-14]
openflex1_to_openvlex2_adapter/openflex1_to_openvlex2_adapter_plate.large.2x2.stl
50.4 x 50.4 x 0.296
