manolitto/openvlex2/socket_negatives/openvlex.bottom_socket_negative.square.3x3.square.stl

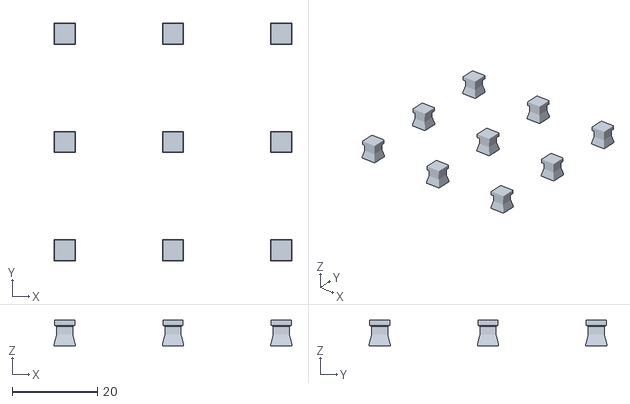
[picture p141: CAD file, 2021-04-16]
socket_negatives/openvlex.bottom_socket_negative.square.3x3.square.stl
55.8 x 55.8 x 6.00
