manolitto/openvlex2/stairs_and_risers/dungeon_stone/curved/dungeon_stone_stairs.curved.inch.platform.4x22.5°.A.stl

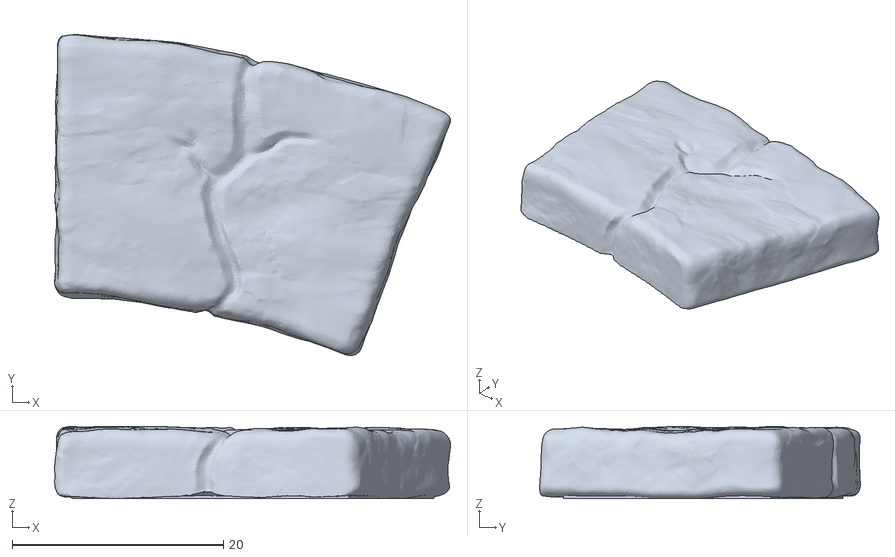
[picture p142: CAD file, 2021-03-27]
stairs_and_risers/dungeon_stone/curved/dungeon_stone_stairs.curved.inch.platform.4x22.5°.A.stl
37.5 x 30.4 x 6.86
