manolitto/openvlex2/stairs_and_risers/plain/plain#riser+square,platform.2x1.openvlex.stl

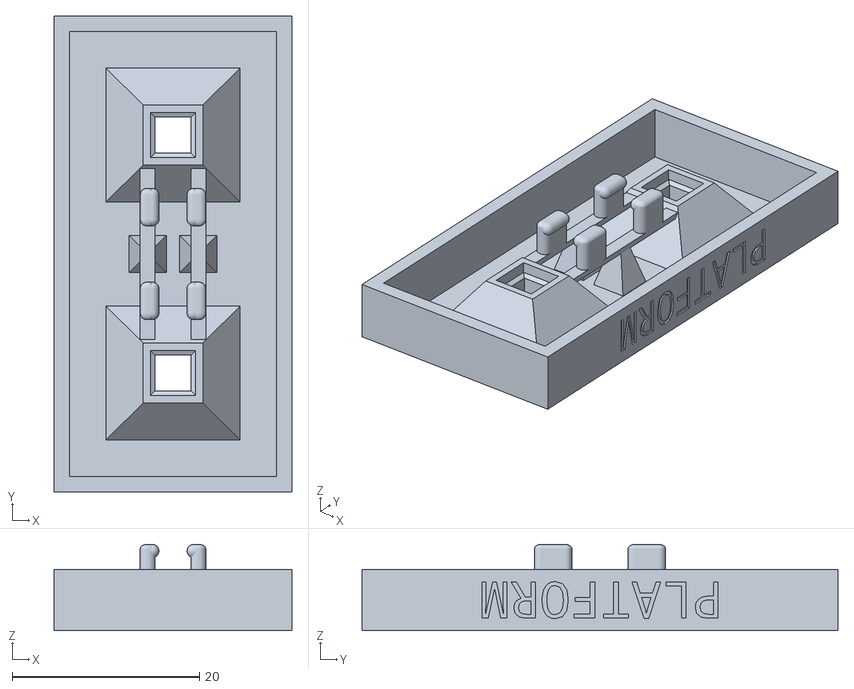
[picture p143: CAD file, 2022-04-11]
stairs_and_risers/plain/plain#riser+square,platform.2x1.openvlex.stl
25.4 x 50.8 x 9.20
