manolitto/openvlex2/bases/plain/magnetic,openlock,openvlex+dual_parts/plain#base+square.4x3.magnetic,openlock,openvlex+upper_part.stl

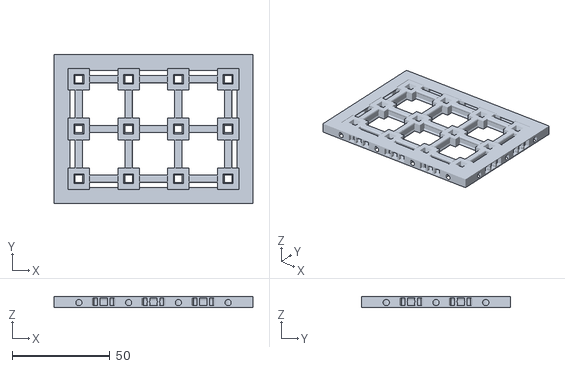
[picture p144: CAD file, 2022-01-04]
bases/plain/magnetic,openlock,openvlex+dual_parts/plain#base+square.4x3.magnetic,openlock,openvlex+upper_part.stl
101.6 x 76.2 x 5.40
