manolitto/openvlex2/bases/plain/magnetic,openlock,openvlex+radial/plain#base+square.2x2.magnetic.openlock,openvlex+radial,lower_part.stl

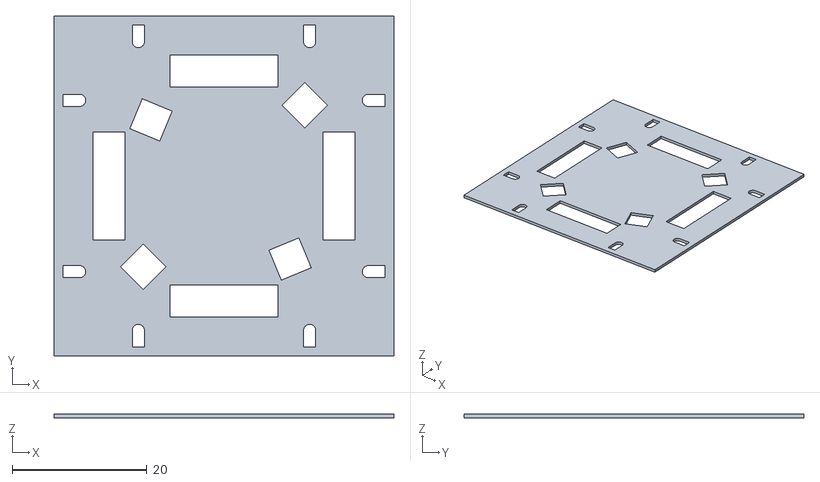
[picture p145: CAD file, 2021-11-02]
bases/plain/magnetic,openlock,openvlex+radial/plain#base+square.2x2.magnetic.openlock,openvlex+radial,lower_part.stl
50.4 x 50.4 x 0.6
