manolitto/openvlex2/gluing-stencil/openvlex_gluing_stencil.3x1.stl

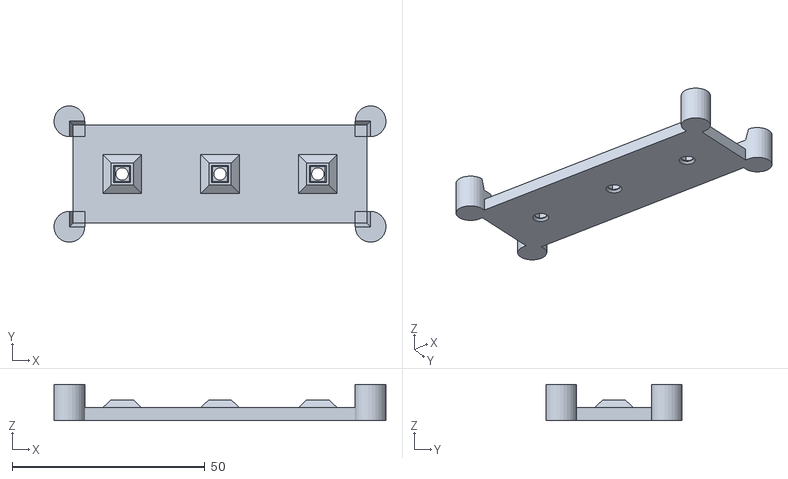
[picture p147: CAD file, 2022-04-11]
gluing-stencil/openvlex_gluing_stencil.3x1.stl
86.2 x 35.4 x 9.40
