manolitto/openvlex2/openflex1_to_openvlex2_adapter/openflex1_to_openvlex2_adapter_plate.large.2x1.stl

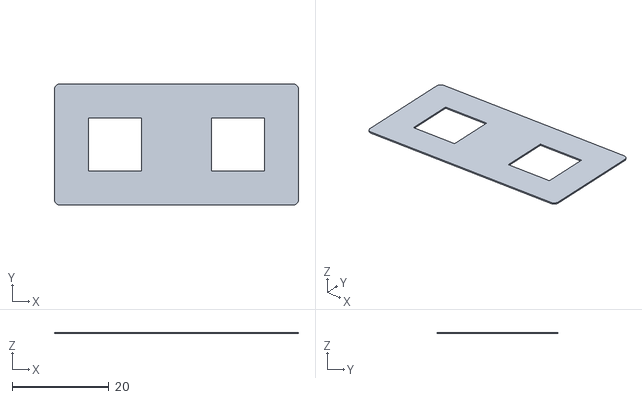
[picture p148: CAD file, 2021-03-14]
openflex1_to_openvlex2_adapter/openflex1_to_openvlex2_adapter_plate.large.2x1.stl
50.4 x 25.0 x 0.296
