manolitto/openvlex2/socket_negatives/openvlex.top_socket_negative.square.4x4.square.stl

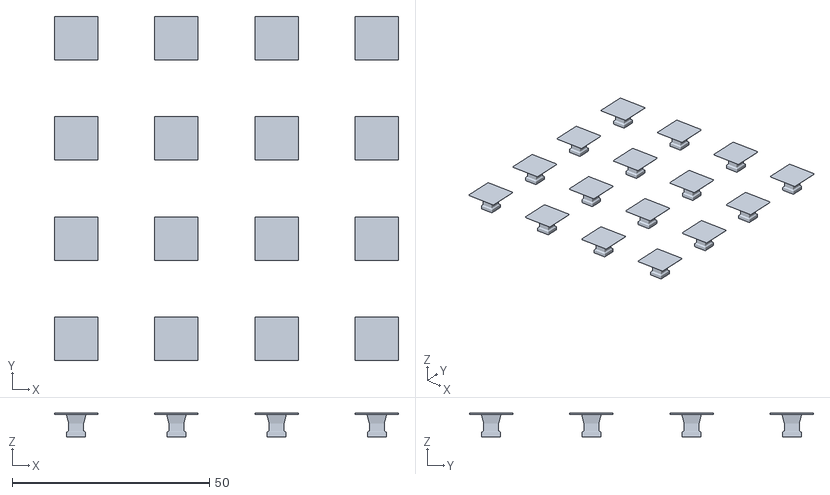
[picture p149: CAD file, 2021-04-16]
socket_negatives/openvlex.top_socket_negative.square.4x4.square.stl
87.2 x 87.2 x 6.00
