manolitto/openvlex2/stairs_and_risers/dungeon_stone/curved/dungeon_stone_stairs.curved.inch.riser.1x90°x0.5.openvlex.radial.stl

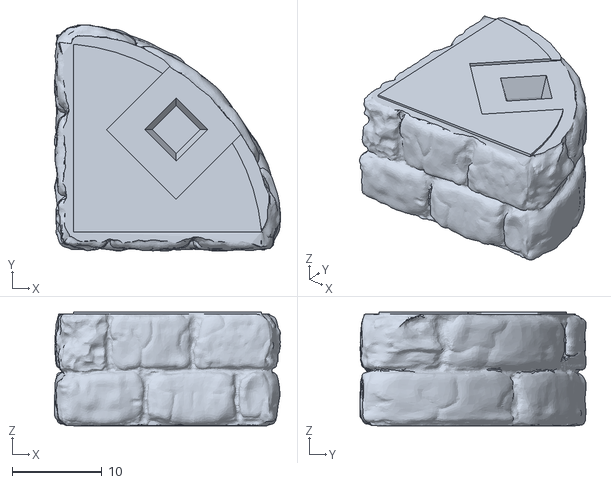
[picture p150: CAD file, 2021-03-27]
stairs_and_risers/dungeon_stone/curved/dungeon_stone_stairs.curved.inch.riser.1x90°x0.5.openvlex.radial.stl
25.2 x 25.3 x 12.7
