manolitto/openvlex2/stairs_and_risers/dungeon_stone/square/dungeon_stone_stairs.square.inch.riser.2x1x0.5.openvlex.stl

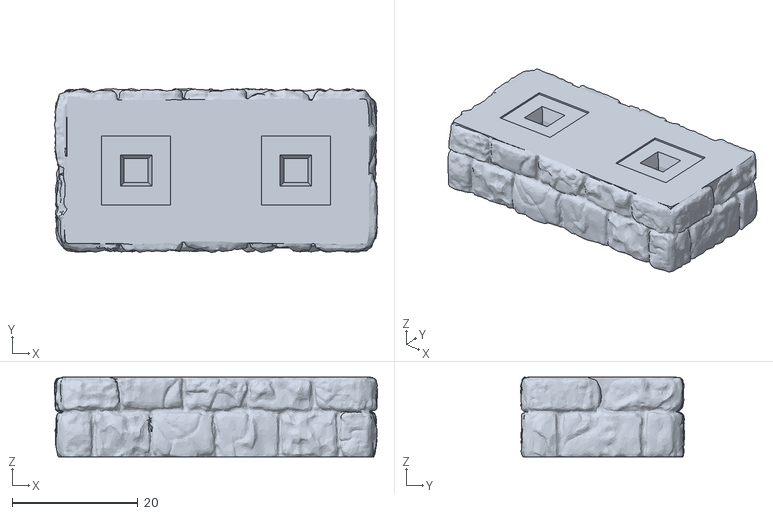
[picture p151: CAD file, 2021-04-06]
stairs_and_risers/dungeon_stone/square/dungeon_stone_stairs.square.inch.riser.2x1x0.5.openvlex.stl
51.3 x 26.0 x 12.7
