manolitto/openvlex2/stairs_and_risers/plain/plain#riser+square,terrain.2x2.openvlex,L-shape.stl

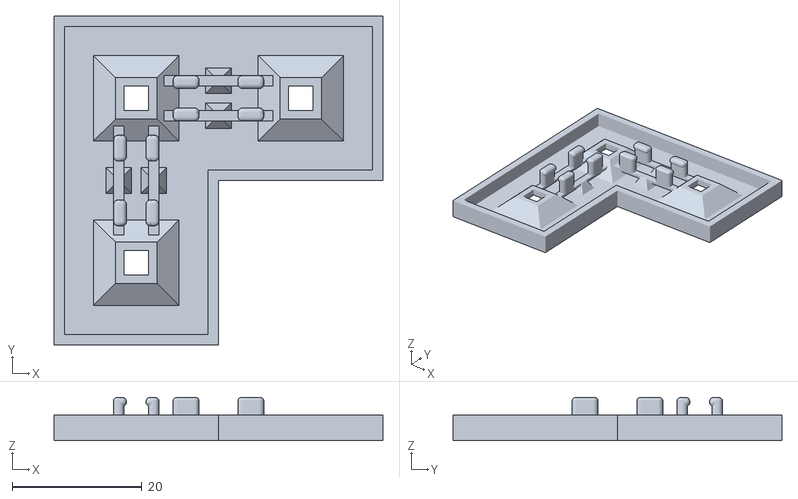
[picture p152: CAD file, 2022-04-11]
stairs_and_risers/plain/plain#riser+square,terrain.2x2.openvlex,L-shape.stl
50.8 x 50.8 x 6.70
