manolitto/openvlex2/bases/dungeon_stone/dungeon_stone#base+square.3x1.openlock,openvlex+edge.stl

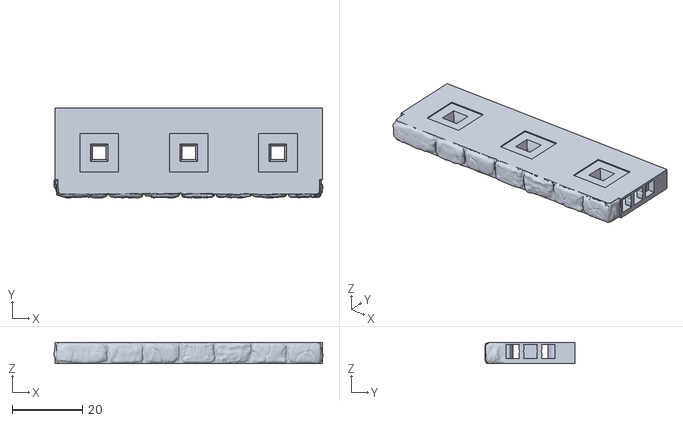
[picture p153: CAD file, 2021-04-17]
bases/dungeon_stone/dungeon_stone#base+square.3x1.openlock,openvlex+edge.stl
76.5 x 25.6 x 6.01
