manolitto/openvlex2/bases/plain/magnetic,openlock,openvlex+dual_parts/plain#base+square.5x4.magnetic,openlock,openvlex+border_only,lower_part.stl

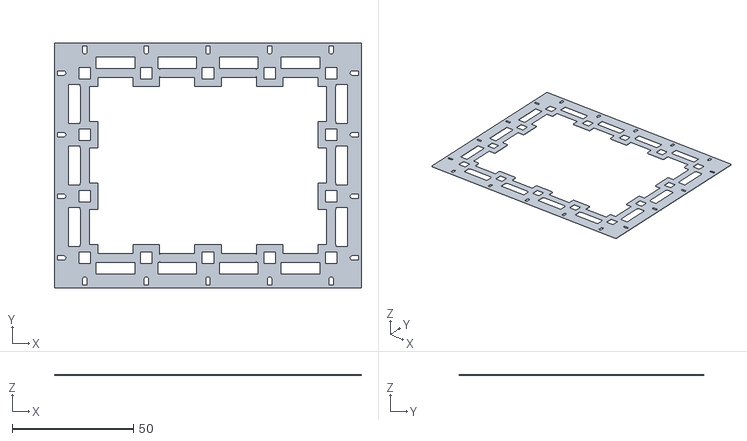
[picture p154: CAD file, 2022-01-04]
bases/plain/magnetic,openlock,openvlex+dual_parts/plain#base+square.5x4.magnetic,openlock,openvlex+border_only,lower_part.stl
126.6 x 101.2 x 0.6
