manolitto/openvlex2/bases/plain/openlock,openvlex/plain#base+square.5x4.openlock,openvlex+border_only.stl

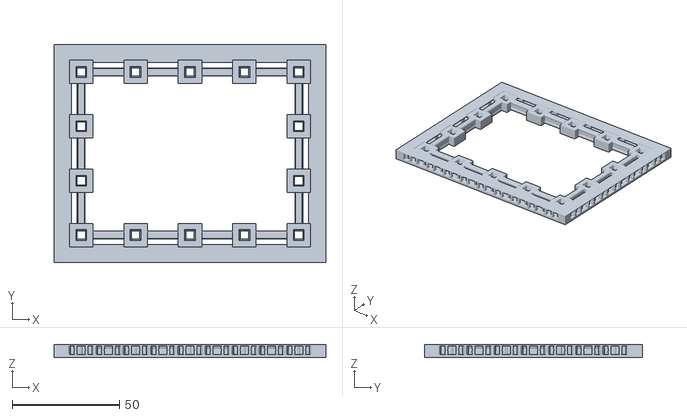
[picture p156: CAD file, 2022-01-04]
bases/plain/openlock,openvlex/plain#base+square.5x4.openlock,openvlex+border_only.stl
127.0 x 101.6 x 6.01
