manolitto/openvlex2/gluing-stencil/openvlex_gluing_stencil.3x2.stl

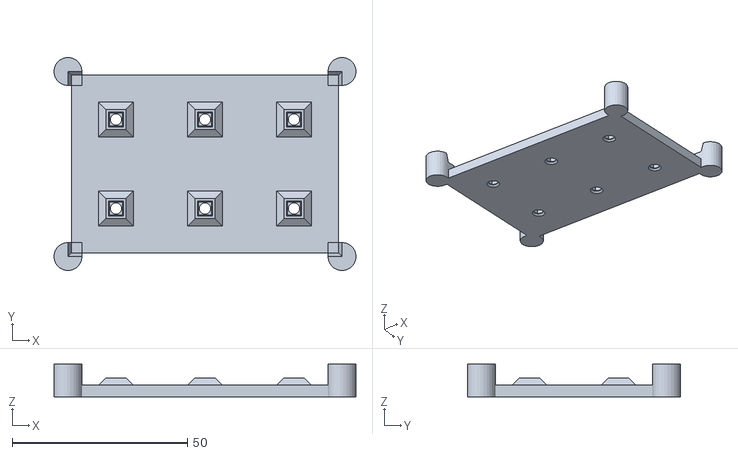
[picture p157: CAD file, 2022-04-11]
gluing-stencil/openvlex_gluing_stencil.3x2.stl
86.2 x 60.8 x 9.40
