manolitto/openvlex2/openflex1_to_openvlex2_adapter/openflex1_to_openvlex2_adapter_plate.small.2x2.stl

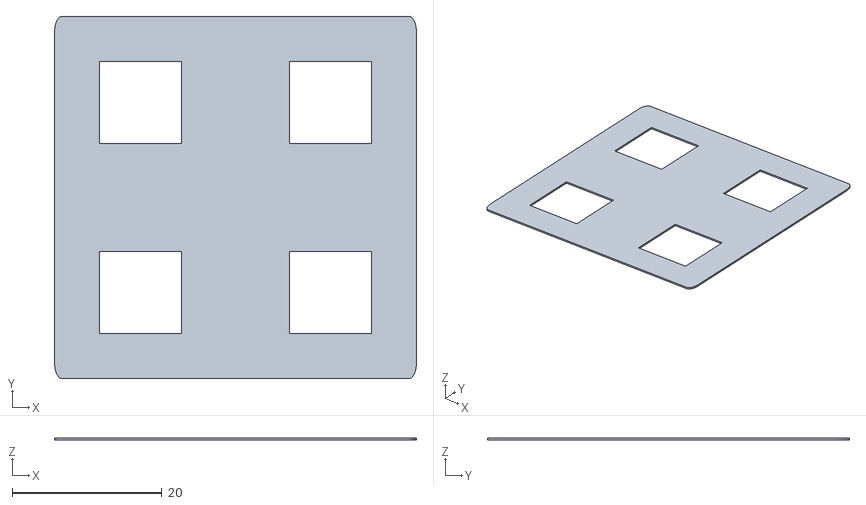
[picture p158: CAD file, 2021-03-14]
openflex1_to_openvlex2_adapter/openflex1_to_openvlex2_adapter_plate.small.2x2.stl
48.4 x 48.4 x 0.296
