manolitto/openvlex2/socket_negatives/openvlex.bottom_socket_negative.square.4x4.square.stl

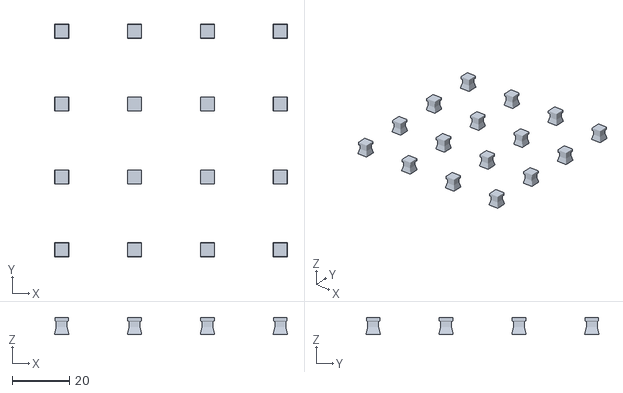
[picture p159: CAD file, 2021-04-16]
socket_negatives/openvlex.bottom_socket_negative.square.4x4.square.stl
81.2 x 81.2 x 6.00
