manolitto/openvlex2/stairs_and_risers/dungeon_stone/curved/dungeon_stone_stairs.curved.inch.platform.4x22.5°.C.stl

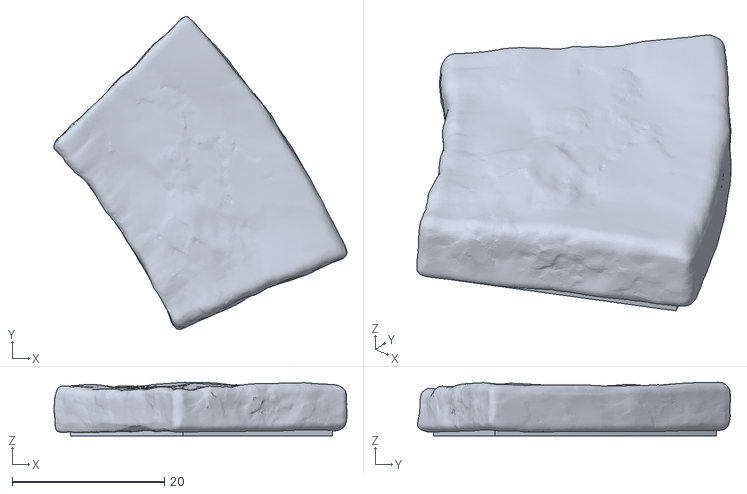
[picture p160: CAD file, 2021-03-27]
stairs_and_risers/dungeon_stone/curved/dungeon_stone_stairs.curved.inch.platform.4x22.5°.C.stl
38.5 x 41.1 x 7.03
