manolitto/openvlex2/stairs_and_risers/dungeon_stone/square/dungeon_stone_stairs.square.inch.riser.1x1x0.3.openvlex.stl

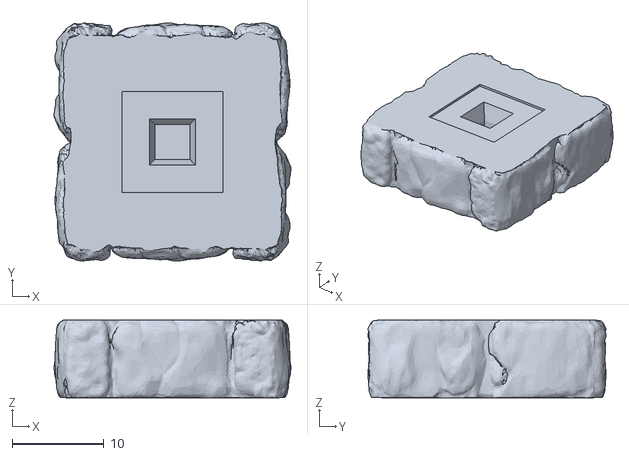
[picture p161: CAD file, 2021-04-06]
stairs_and_risers/dungeon_stone/square/dungeon_stone_stairs.square.inch.riser.1x1x0.3.openvlex.stl
25.9 x 26.0 x 8.47
