manolitto/openvlex2/stairs_and_risers/plain/plain#riser+square,terrain.2x1.openvlex.stl

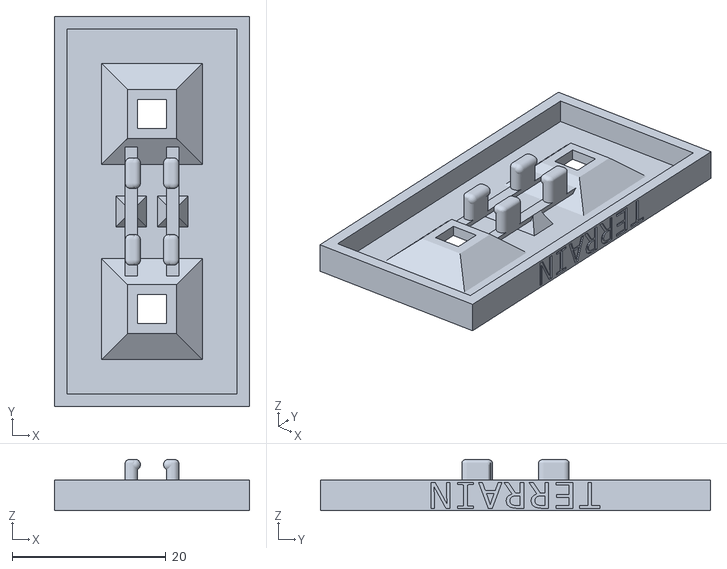
[picture p162: CAD file, 2022-04-11]
stairs_and_risers/plain/plain#riser+square,terrain.2x1.openvlex.stl
25.4 x 50.8 x 6.70
