manolitto/openvlex2/bases/plain/magnetic,openlock,openvlex+dual_parts/plain#base+square.5x2.magnetic,openlock,openvlex+upper_part.stl

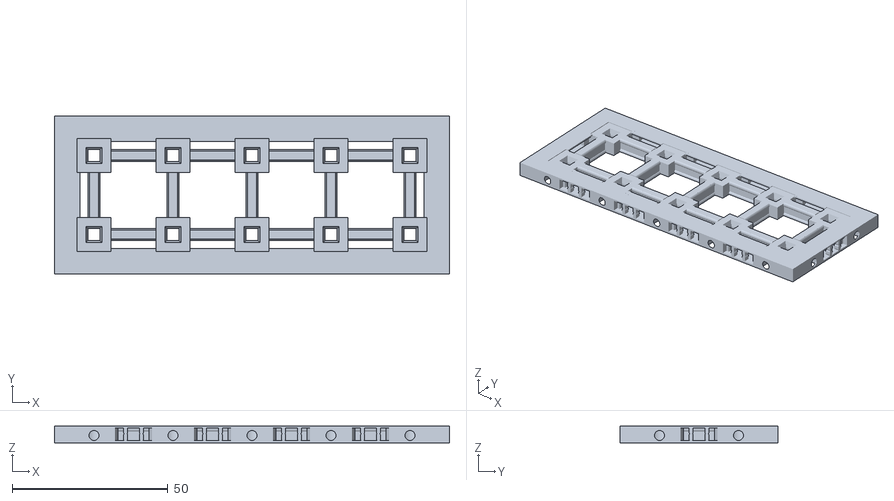
[picture p163: CAD file, 2022-01-04]
bases/plain/magnetic,openlock,openvlex+dual_parts/plain#base+square.5x2.magnetic,openlock,openvlex+upper_part.stl
127.0 x 50.8 x 5.40
