manolitto/openvlex2/bases/plain/openlock,openvlex/plain#base+square.4x3.openlock,openvlex+border_only.stl

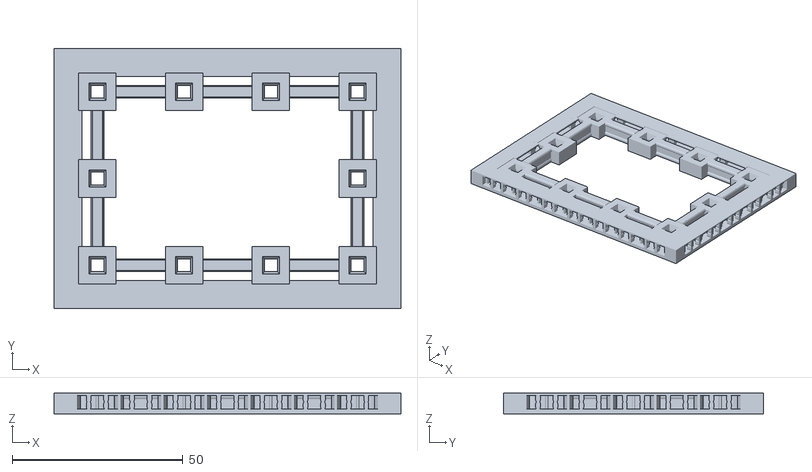
[picture p164: CAD file, 2022-01-04]
bases/plain/openlock,openvlex/plain#base+square.4x3.openlock,openvlex+border_only.stl
101.6 x 76.2 x 6.01
