manolitto/openvlex2/gluing-stencil/openvlex_gluing_stencil.3x3.stl

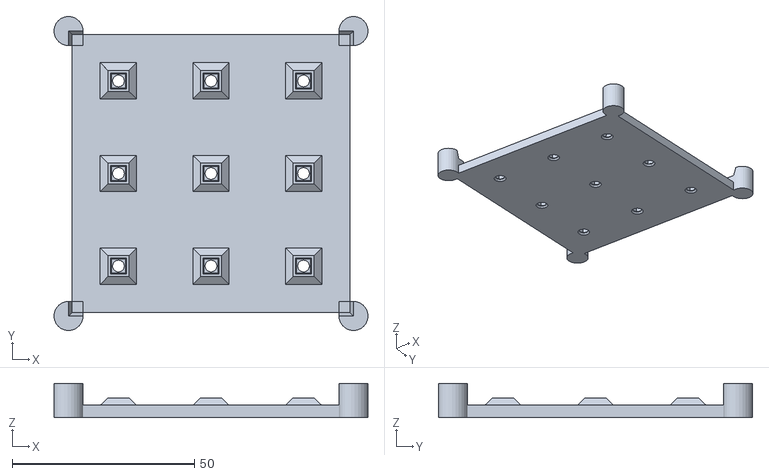
[picture p165: CAD file, 2022-04-11]
gluing-stencil/openvlex_gluing_stencil.3x3.stl
86.2 x 86.2 x 9.40
