manolitto/openvlex2/socket_negatives/openvlex.top_socket_negative.square.3x3.square.stl

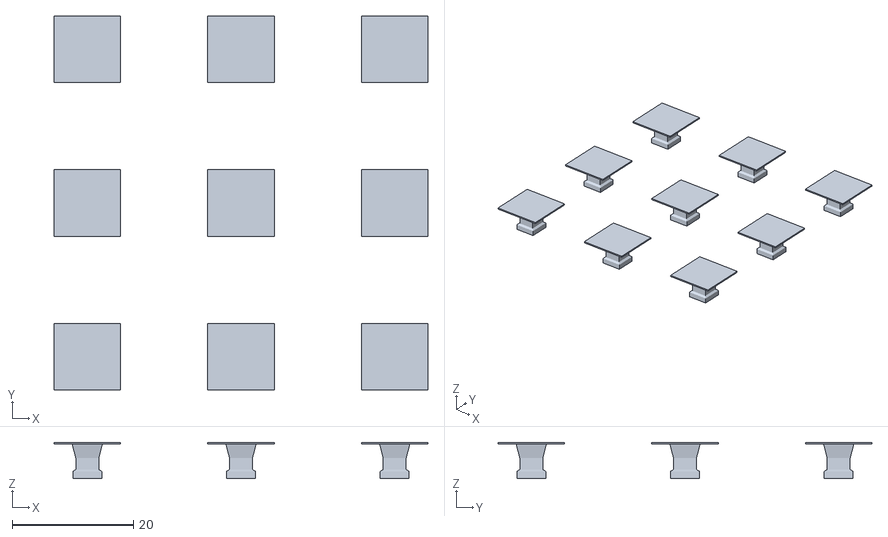
[picture p166: CAD file, 2021-04-16]
socket_negatives/openvlex.top_socket_negative.square.3x3.square.stl
61.8 x 61.8 x 6.00
