manolitto/openvlex2/stairs_and_risers/dungeon_stone/curved/dungeon_stone_stairs.curved.inch.platform.4x22.5°.D.stl

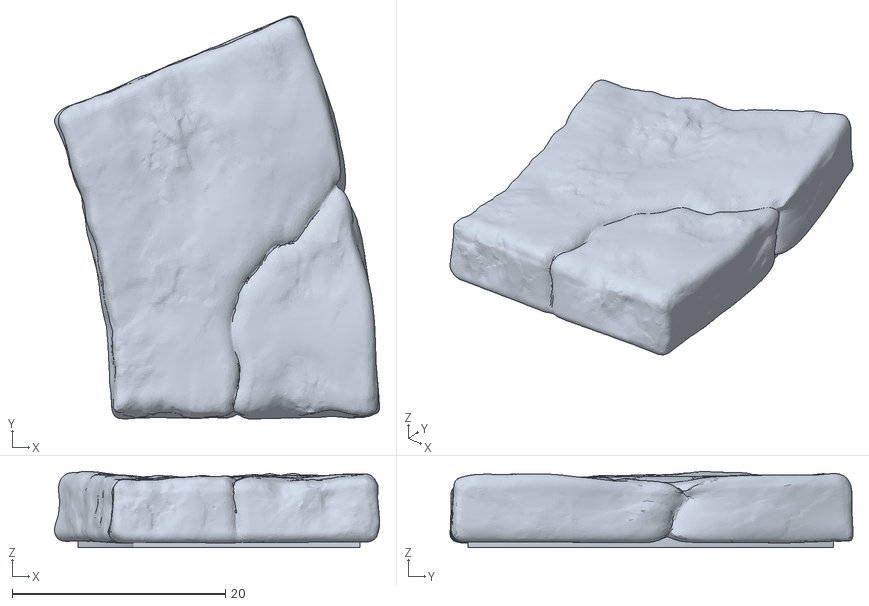
[picture p167: CAD file, 2021-03-27]
stairs_and_risers/dungeon_stone/curved/dungeon_stone_stairs.curved.inch.platform.4x22.5°.D.stl
30.5 x 37.7 x 7.15
