manolitto/openvlex2/stairs_and_risers/plain/plain#riser+square,half_inch_support.2x1.openvlex.stl

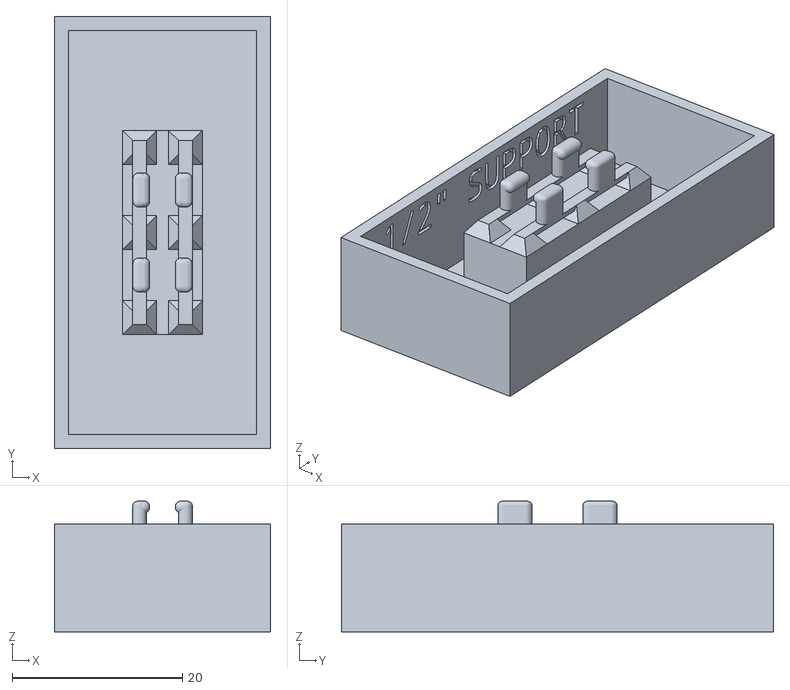
[picture p169: CAD file, 2022-01-11]
stairs_and_risers/plain/plain#riser+square,half_inch_support.2x1.openvlex.stl
25.4 x 50.8 x 15.4
