manolitto/openvlex2/bases/dungeon_stone/dungeon_stone#base+square.2x1.openlock,openvlex+edge.stl

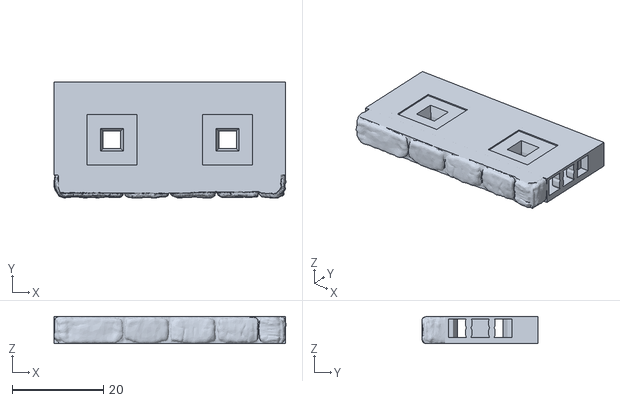
[picture p170: CAD file, 2021-04-17]
bases/dungeon_stone/dungeon_stone#base+square.2x1.openlock,openvlex+edge.stl
50.9 x 25.5 x 6.01
