manolitto/openvlex2/bases/plain/magnetic,openlock,openvlex+dual_parts/plain#base+square.6x6.magnetic,openlock,openvlex+lower_part.stl

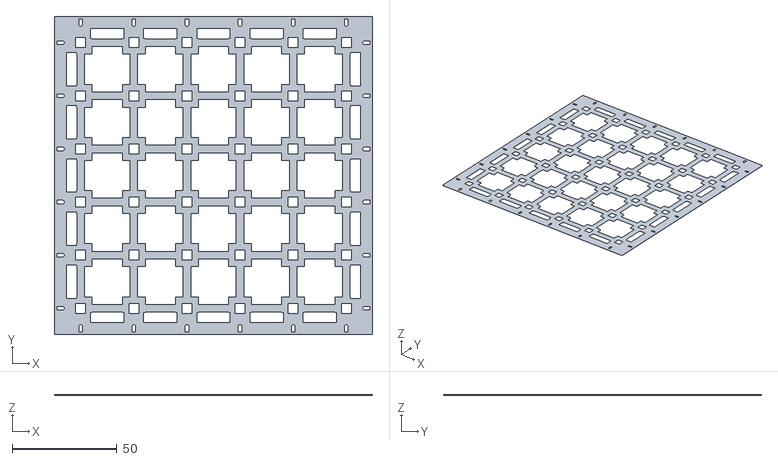
[picture p171: CAD file, 2022-01-04]
bases/plain/magnetic,openlock,openvlex+dual_parts/plain#base+square.6x6.magnetic,openlock,openvlex+lower_part.stl
152.0 x 152.0 x 0.6
