manolitto/openvlex2/bases/plain/openlock,openvlex/plain#base+square.8x6.openlock,openvlex+border_only.stl

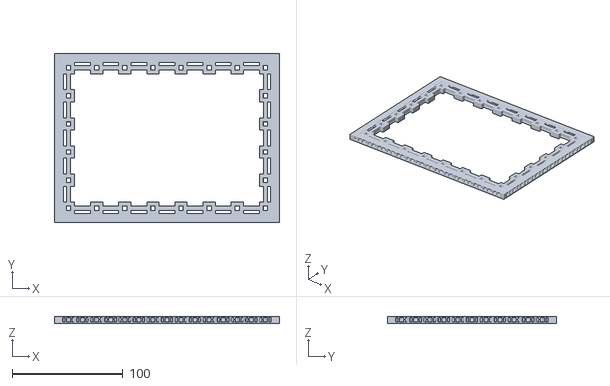
[picture p173: CAD file, 2022-01-04]
bases/plain/openlock,openvlex/plain#base+square.8x6.openlock,openvlex+border_only.stl
203.2 x 152.4 x 6.01
