manolitto/openvlex2/gluing-stencil/openvlex_gluing_stencil.1x1.stl

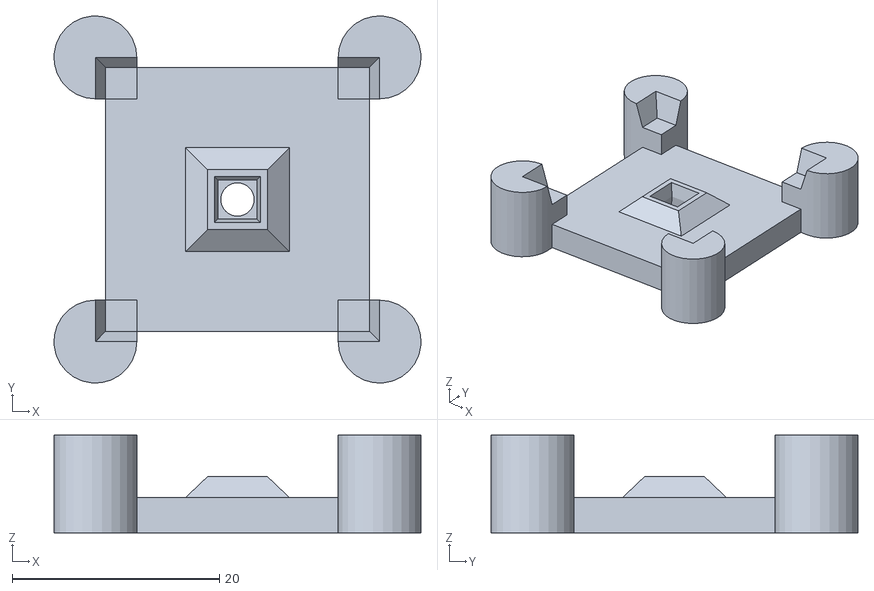
[picture p174: CAD file, 2022-04-11]
gluing-stencil/openvlex_gluing_stencil.1x1.stl
35.4 x 35.4 x 9.40
