manolitto/openvlex2/socket_negatives/openvlex.top_socket_negative.square.3x2.square.stl

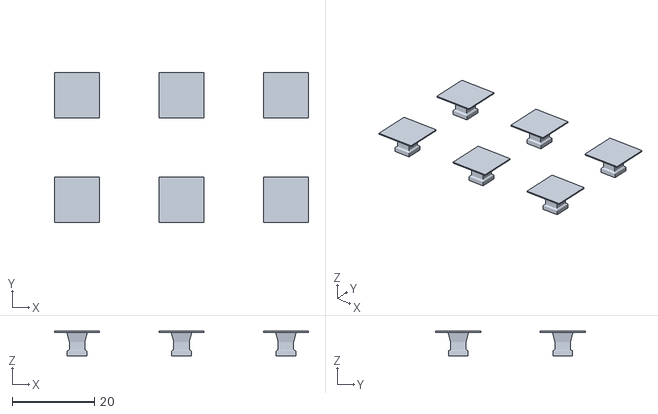
[picture p175: CAD file, 2021-04-16]
socket_negatives/openvlex.top_socket_negative.square.3x2.square.stl
61.8 x 36.4 x 6.00
