manolitto/openvlex2/stairs_and_risers/dungeon_stone/curved/dungeon_stone_stairs.curved.inch.platform.4x22.5°.B.stl

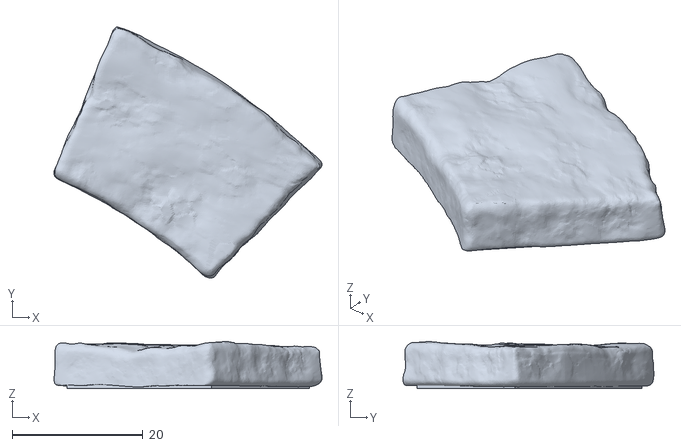
[picture p176: CAD file, 2021-03-27]
stairs_and_risers/dungeon_stone/curved/dungeon_stone_stairs.curved.inch.platform.4x22.5°.B.stl
41.0 x 38.4 x 7.20
