manolitto/openvlex2/stairs_and_risers/dungeon_stone/square/dungeon_stone_stairs.square.inch.riser.1x1x0.5.openvlex.stl

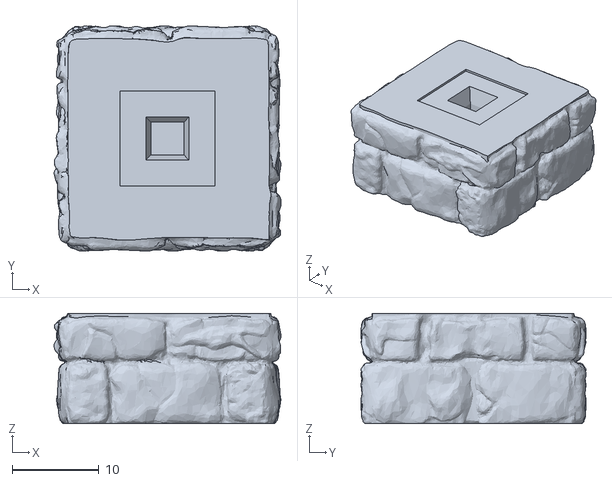
[picture p177: CAD file, 2021-04-06]
stairs_and_risers/dungeon_stone/square/dungeon_stone_stairs.square.inch.riser.1x1x0.5.openvlex.stl
26.2 x 26.0 x 12.7
