manolitto/openvlex2/stairs_and_risers/plain/plain#riser+square,low.2x1.openvlex.stl

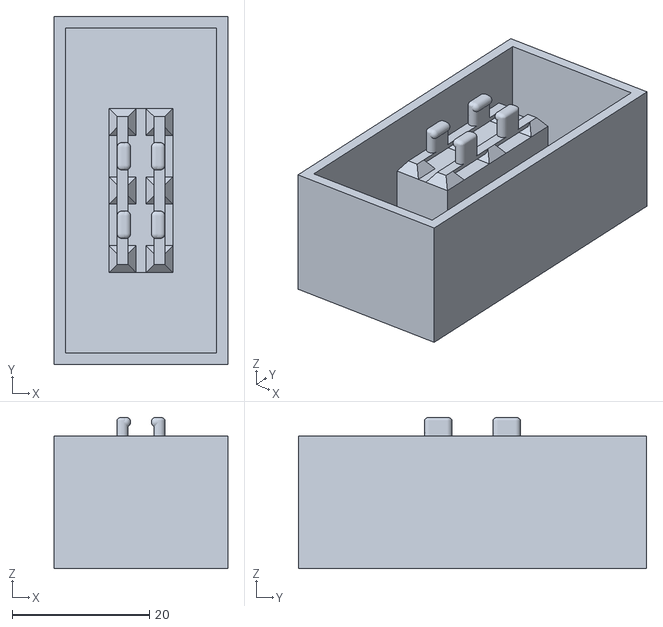
[picture p178: CAD file, 2022-01-11]
stairs_and_risers/plain/plain#riser+square,low.2x1.openvlex.stl
25.4 x 50.8 x 22.1
