manolitto/openvlex2/bases/plain/magnetic,openlock,openvlex+single_part/plain#base+square.1x1.magnetic,openlock,MOOO,openvlex+single_part.stl

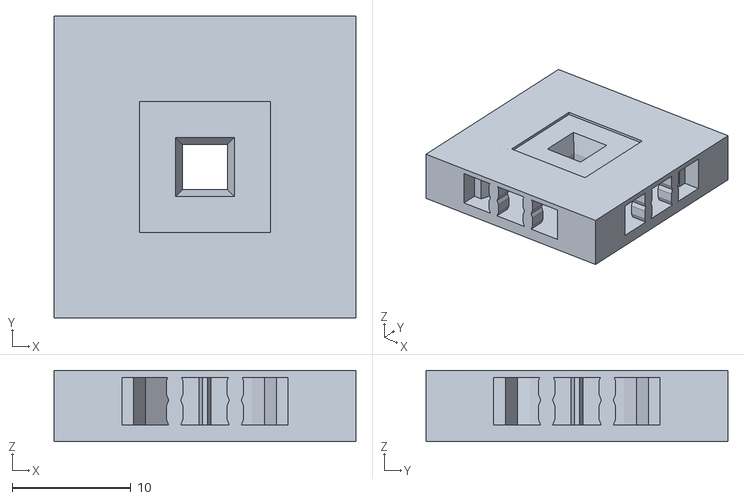
[picture p180: CAD file, 2022-04-11]
bases/plain/magnetic,openlock,openvlex+single_part/plain#base+square.1x1.magnetic,openlock,MOOO,openvlex+single_part.stl
25.4 x 25.4 x 6.01
