manolitto/openvlex2/bases/plain/openlock,openvlex/plain#base+square.5x3.openlock,openvlex+border_only.stl

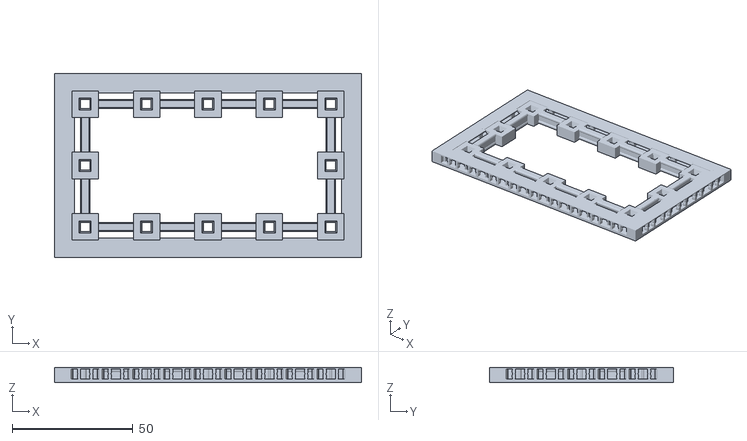
[picture p181: CAD file, 2022-01-04]
bases/plain/openlock,openvlex/plain#base+square.5x3.openlock,openvlex+border_only.stl
127.0 x 76.2 x 6.01
