manolitto/openvlex2/gluing-stencil/openvlex_gluing_stencil.2x1.stl

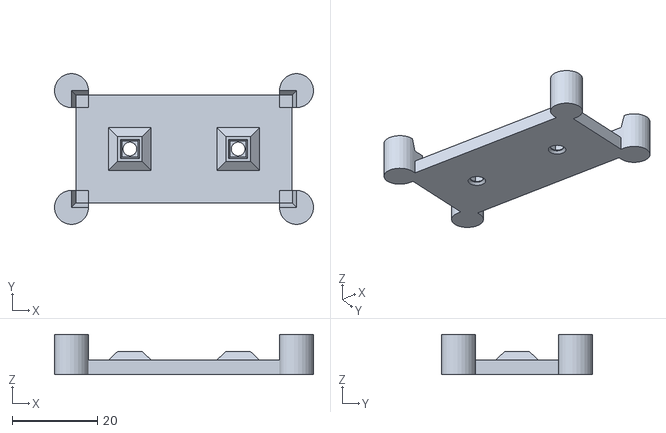
[picture p182: CAD file, 2022-04-11]
gluing-stencil/openvlex_gluing_stencil.2x1.stl
60.8 x 35.4 x 9.40
