manolitto/openvlex2/socket_negatives/openvlex.bottom_socket_negative.square.4x1.square.stl

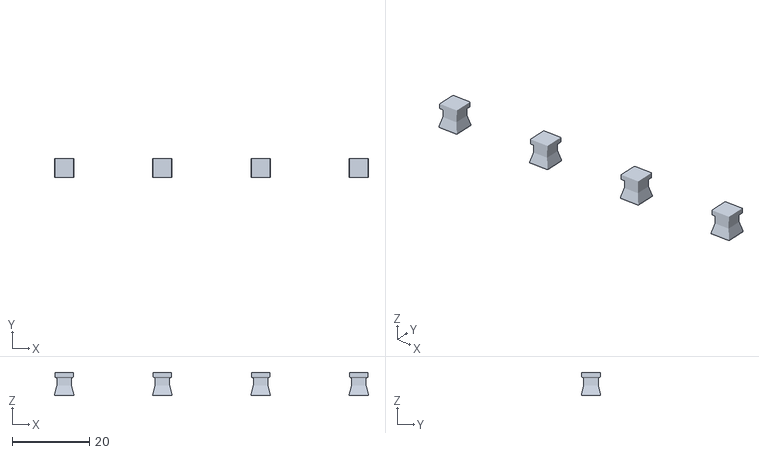
[picture p183: CAD file, 2021-04-16]
socket_negatives/openvlex.bottom_socket_negative.square.4x1.square.stl
81.2 x 5.00 x 6.00
