manolitto/openvlex2/stairs_and_risers/dungeon_stone/curved/dungeon_stone_stairs.curved.inch.riser.3+4x90°x0.5.openvlex.radial.stl

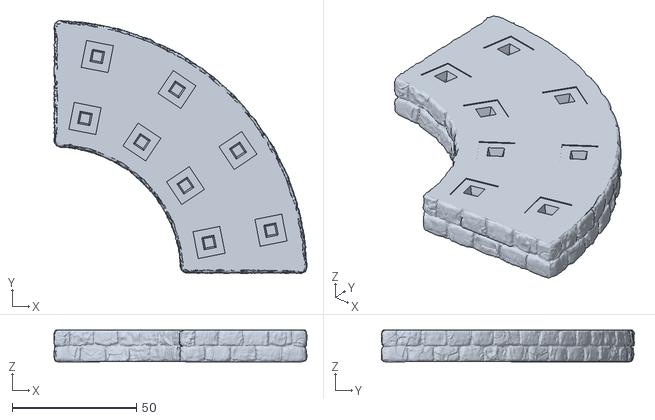
[picture p184: CAD file, 2021-03-20]
stairs_and_risers/dungeon_stone/curved/dungeon_stone_stairs.curved.inch.riser.3+4x90°x0.5.openvlex.radial.stl
101.8 x 101.7 x 12.7
