manolitto/openvlex2/stairs_and_risers/dungeon_stone/square/dungeon_stone_stairs.square.inch.riser.2x2x1.0.openvlex.stl

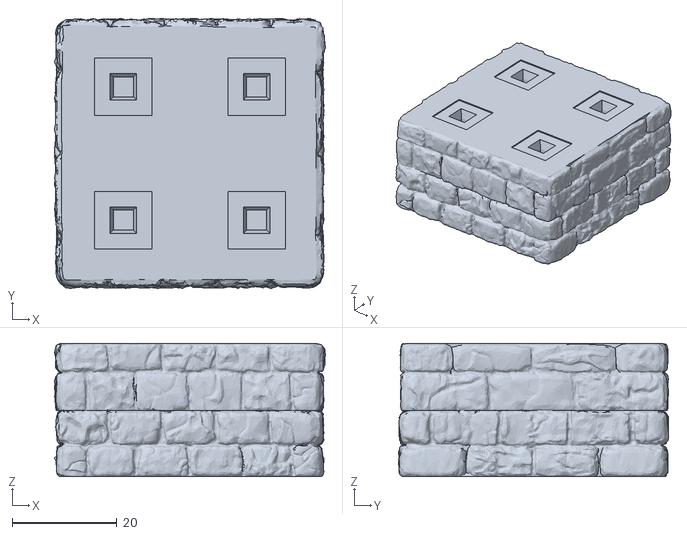
[picture p185: CAD file, 2021-04-06]
stairs_and_risers/dungeon_stone/square/dungeon_stone_stairs.square.inch.riser.2x2x1.0.openvlex.stl
51.7 x 51.4 x 25.4
