manolitto/openvlex2/stairs_and_risers/plain/plain#riser+square,half_inch_support.2x2.openvlex.stl

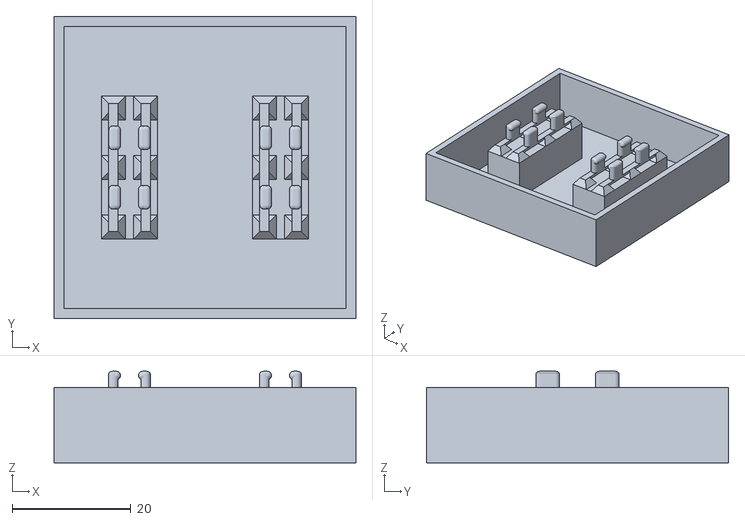
[picture p186: CAD file, 2022-01-11]
stairs_and_risers/plain/plain#riser+square,half_inch_support.2x2.openvlex.stl
50.8 x 50.8 x 15.4
