manolitto/openvlex2/bases/plain/openlock,openvlex/plain#base+square.7x4.openlock,openvlex+border_only.stl

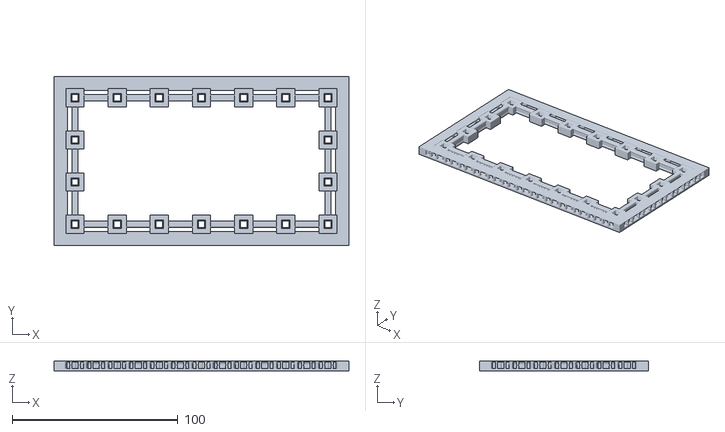
[picture p189: CAD file, 2022-01-04]
bases/plain/openlock,openvlex/plain#base+square.7x4.openlock,openvlex+border_only.stl
177.8 x 101.6 x 6.01
