manolitto/openvlex2/socket_negatives/openvlex.bottom_socket_negative.square.3x1.square.stl

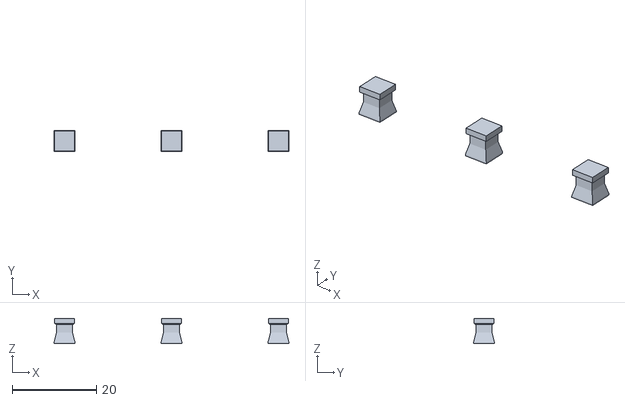
[picture p191: CAD file, 2021-04-16]
socket_negatives/openvlex.bottom_socket_negative.square.3x1.square.stl
55.8 x 5.00 x 6.00
