manolitto/openvlex2/stairs_and_risers/dungeon_stone/curved/dungeon_stone_stairs.curved.inch.platform.2x45°.B.stl

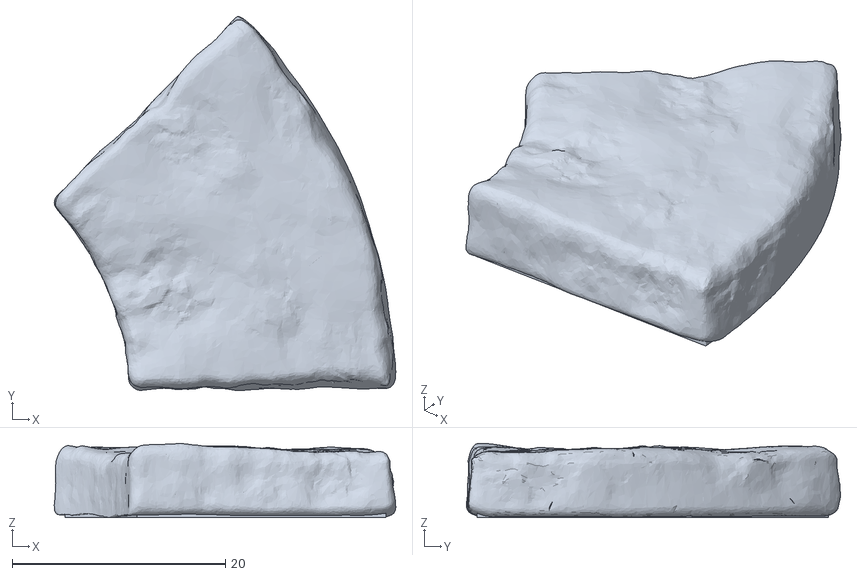
[picture p192: CAD file, 2021-03-20]
stairs_and_risers/dungeon_stone/curved/dungeon_stone_stairs.curved.inch.platform.2x45°.B.stl
32.0 x 35.1 x 6.97
