manolitto/openvlex2/stairs_and_risers/dungeon_stone/square/dungeon_stone_stairs.square.inch.riser.2x1x1.0.openvlex.stl

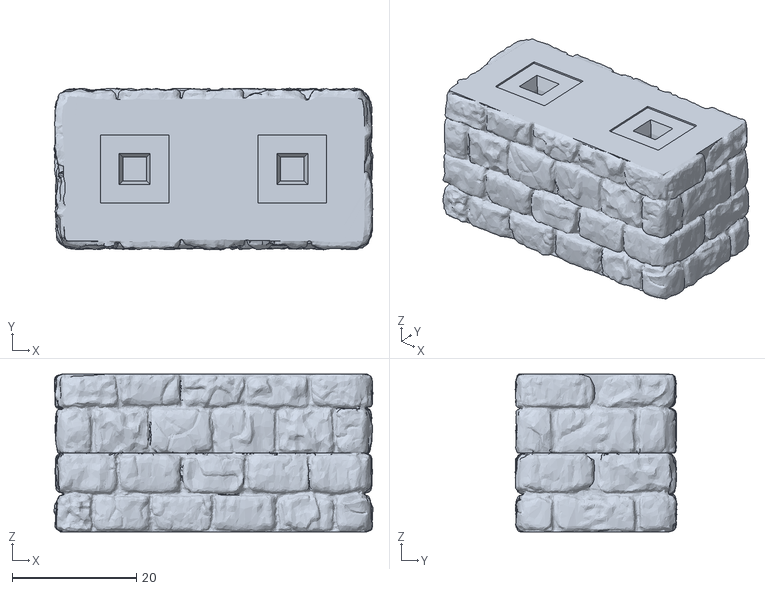
[picture p193: CAD file, 2021-04-06]
stairs_and_risers/dungeon_stone/square/dungeon_stone_stairs.square.inch.riser.2x1x1.0.openvlex.stl
51.4 x 26.1 x 25.4
