manolitto/openvlex2/stairs_and_risers/plain/plain#riser+square,low.2x2.openvlex.stl

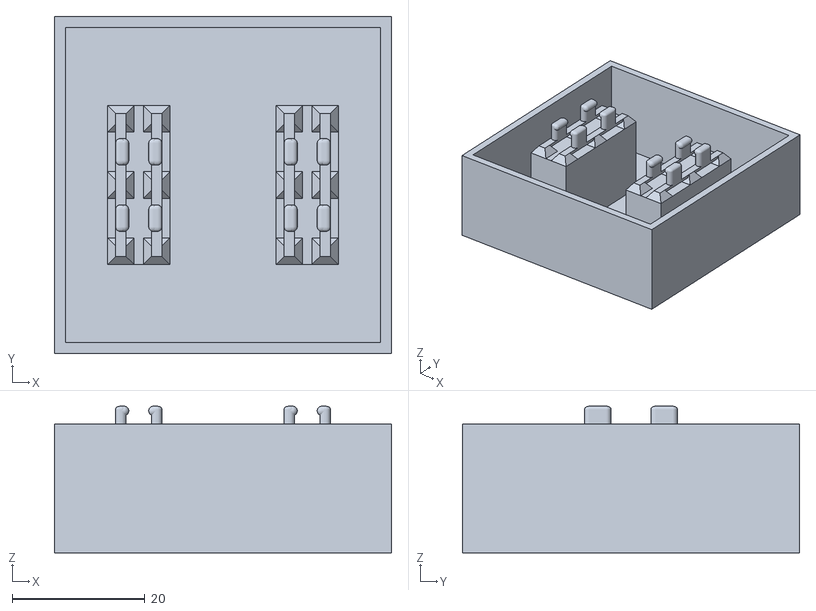
[picture p194: CAD file, 2022-01-11]
stairs_and_risers/plain/plain#riser+square,low.2x2.openvlex.stl
50.8 x 50.8 x 22.1
