manolitto/openvlex2/bases/plain/openlock,openvlex/plain#base+square.8x4.openlock,openvlex+border_only.stl

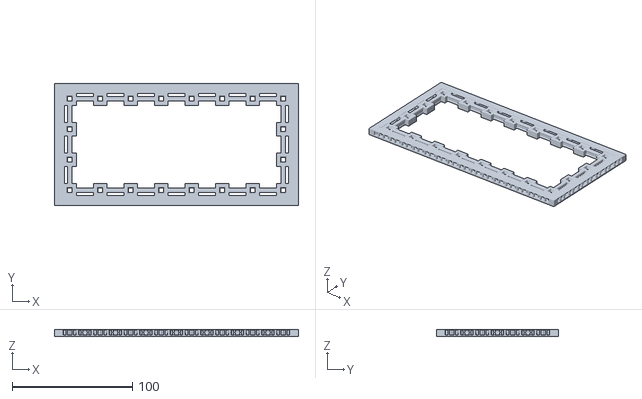
[picture p196: CAD file, 2022-01-04]
bases/plain/openlock,openvlex/plain#base+square.8x4.openlock,openvlex+border_only.stl
203.2 x 101.6 x 6.01
