manolitto/openvlex2/socket_negatives/openvlex.top_socket_negative.square.3x1.square.stl

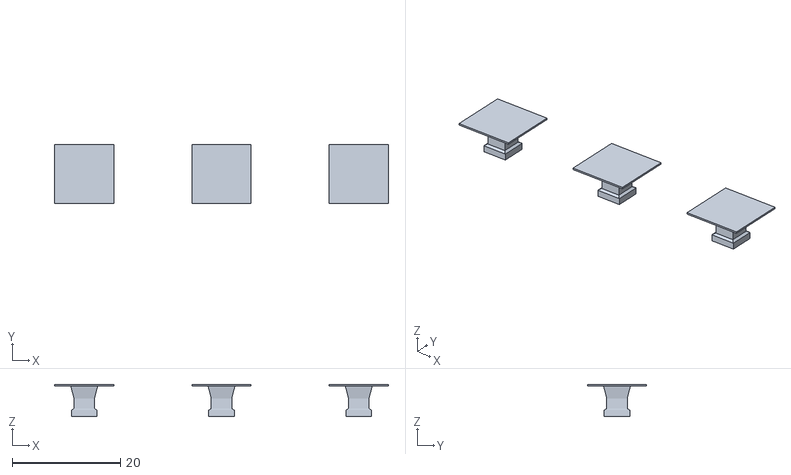
[picture p197: CAD file, 2021-04-16]
socket_negatives/openvlex.top_socket_negative.square.3x1.square.stl
61.8 x 11.0 x 6.00
