manolitto/openvlex2/stairs_and_risers/dungeon_stone/curved/dungeon_stone_stairs.curved.inch.platform.1x90°.stl

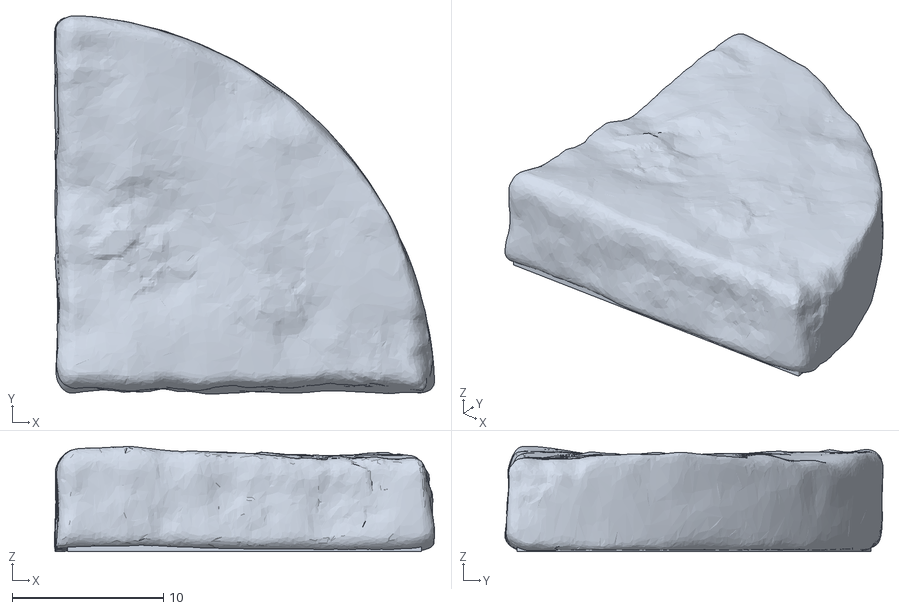
[picture p198: CAD file, 2021-03-20]
stairs_and_risers/dungeon_stone/curved/dungeon_stone_stairs.curved.inch.platform.1x90°.stl
25.1 x 25.0 x 6.98
