manolitto/openvlex2/stairs_and_risers/dungeon_stone/square/dungeon_stone_stairs.square.inch.riser.2x2x0.3.openvlex.stl

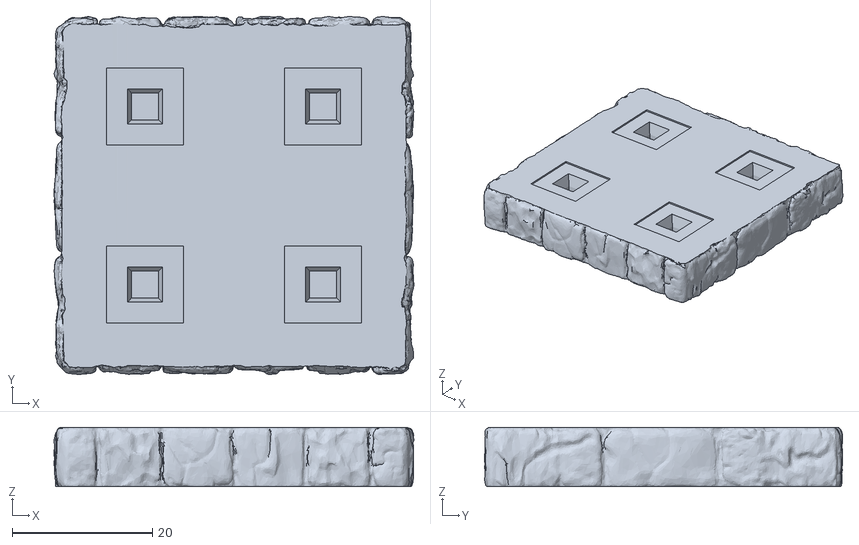
[picture p199: CAD file, 2021-04-06]
stairs_and_risers/dungeon_stone/square/dungeon_stone_stairs.square.inch.riser.2x2x0.3.openvlex.stl
51.3 x 51.1 x 8.47
