manolitto/openvlex2/stairs_and_risers/plain/plain#riser+square,interlayer_half.2x2.openvlex,L-shape.stl

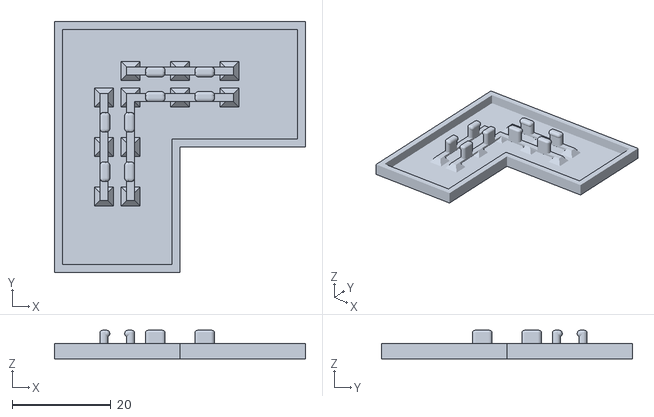
[picture p200: CAD file, 2022-01-10]
stairs_and_risers/plain/plain#riser+square,interlayer_half.2x2.openvlex,L-shape.stl
50.8 x 50.8 x 5.80
