manolitto/openvlex2/bases/plain/magnetic,openlock,openvlex+dual_parts/plain#base+square.6x1.magnetic,openlock,openvlex+upper_part.stl

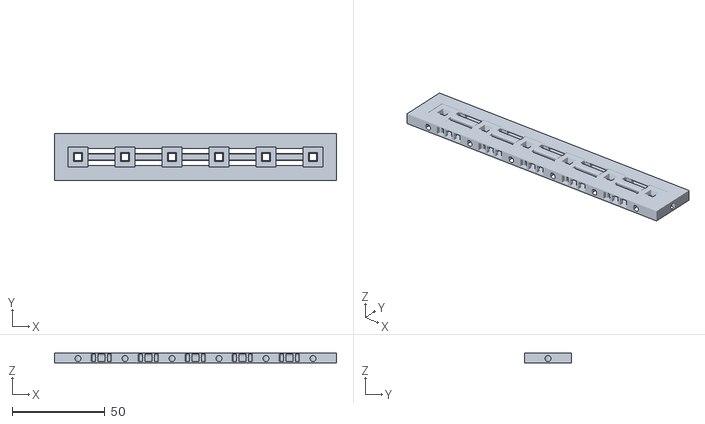
[picture p201: CAD file, 2022-01-04]
bases/plain/magnetic,openlock,openvlex+dual_parts/plain#base+square.6x1.magnetic,openlock,openvlex+upper_part.stl
152.4 x 25.4 x 5.40
